JulianSilva2001/PCB-Defects-Detetion-Device/Documentation/CompDefects_live.png

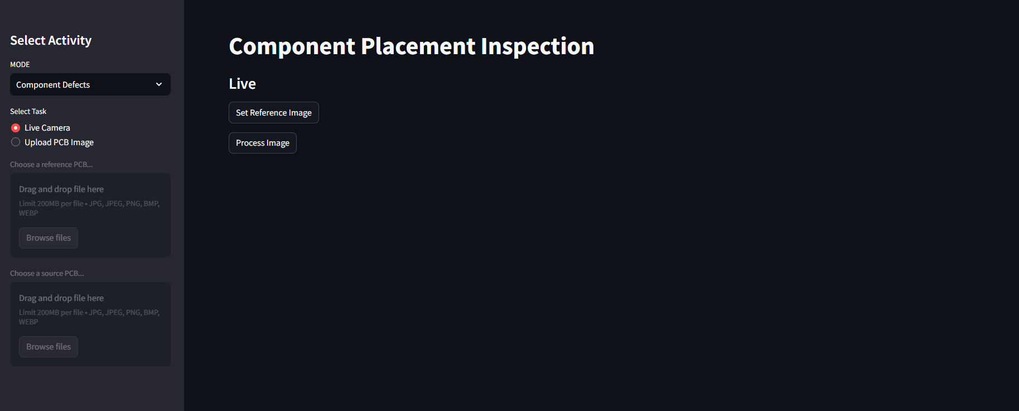
Documentation/CompDefects_live.png
