JulianSilva2001/PCB-Defects-Detetion-Device/Documentation/CompDefects_upload.png

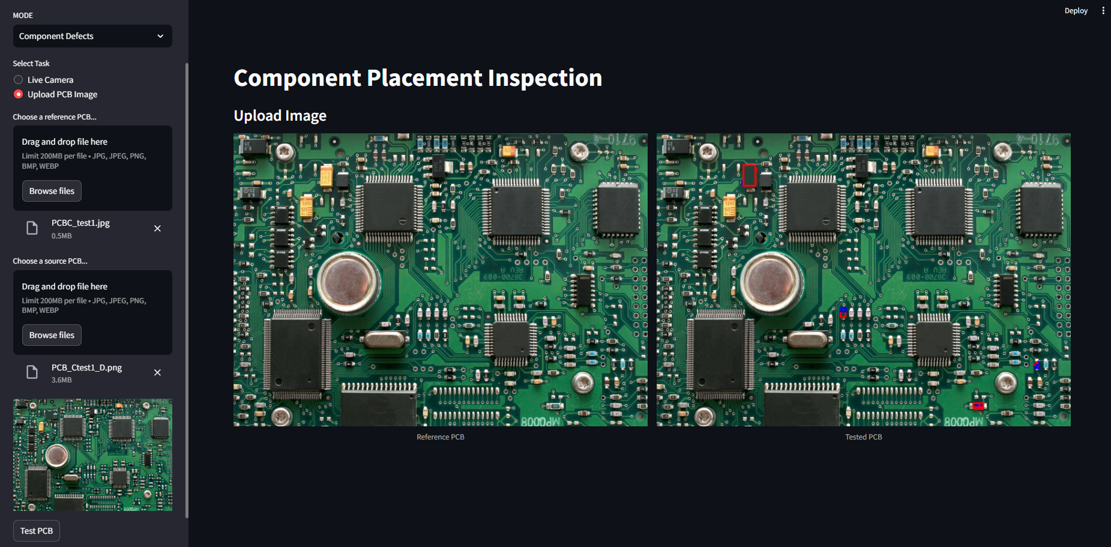
Documentation/CompDefects_upload.png
