JulianSilva2001/PCB-Defects-Detetion-Device/Documentation/Conceptual Design/Enclosure/Enclosure Design A1.jpg

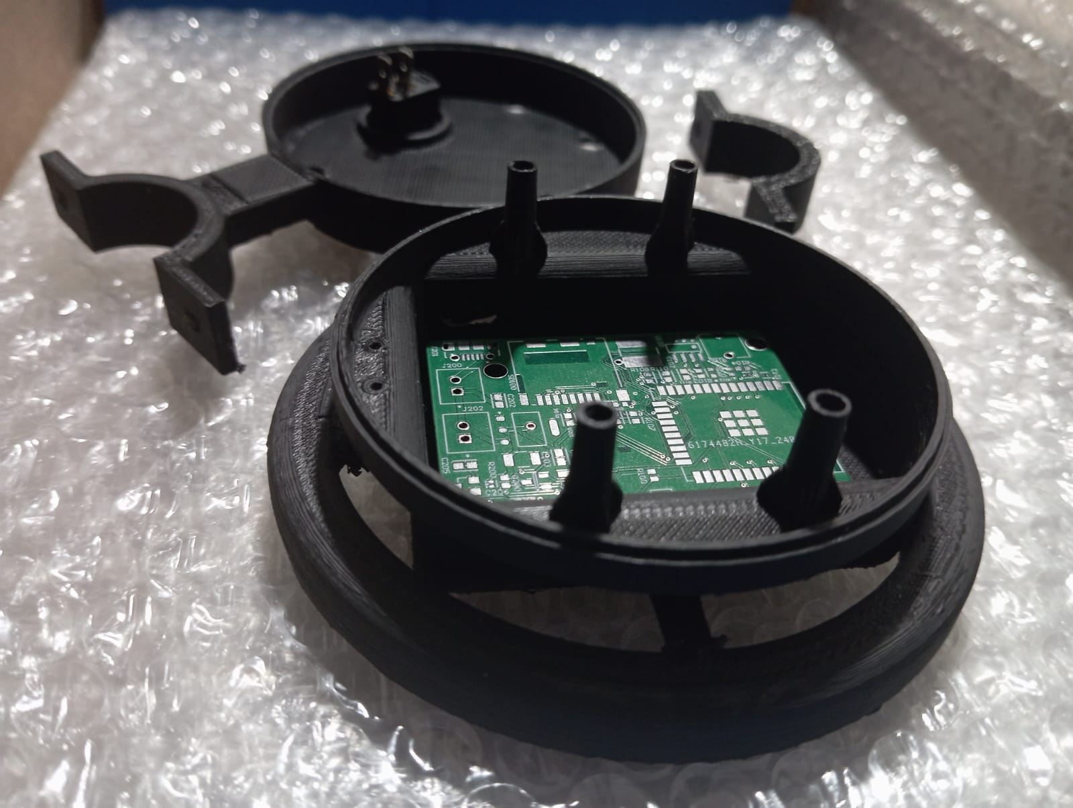
Documentation/Conceptual Design/Enclosure/Enclosure Design A1.jpg
