JulianSilva2001/PCB-Defects-Detetion-Device/Documentation/Conceptual Design/Enclosure/Enclosure Design A4.jpg

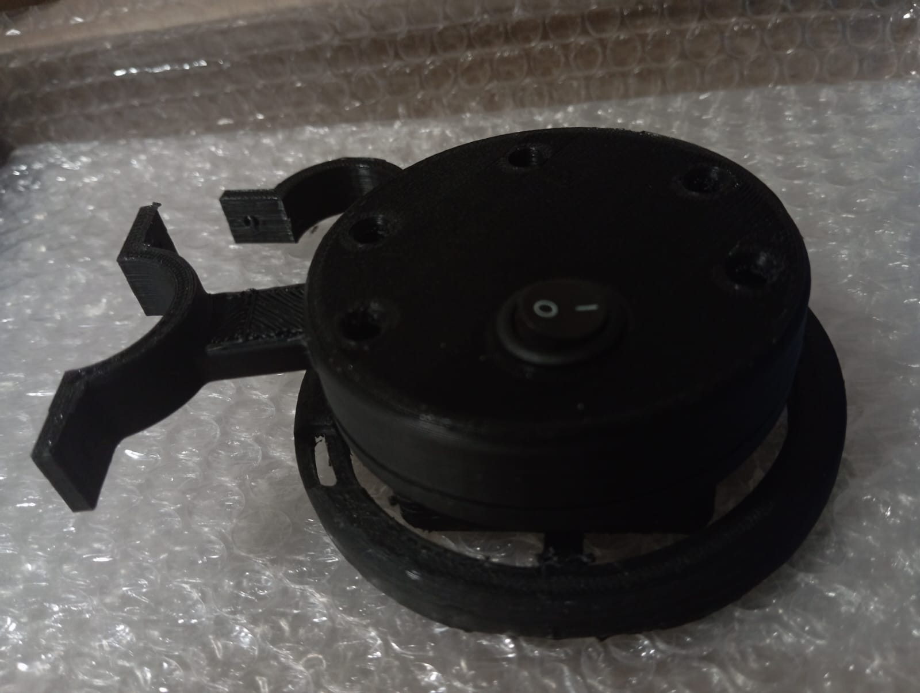
Documentation/Conceptual Design/Enclosure/Enclosure Design A4.jpg
