JulianSilva2001/PCB-Defects-Detetion-Device/Documentation/Conceptual Design/Enclosure/sign.jpg

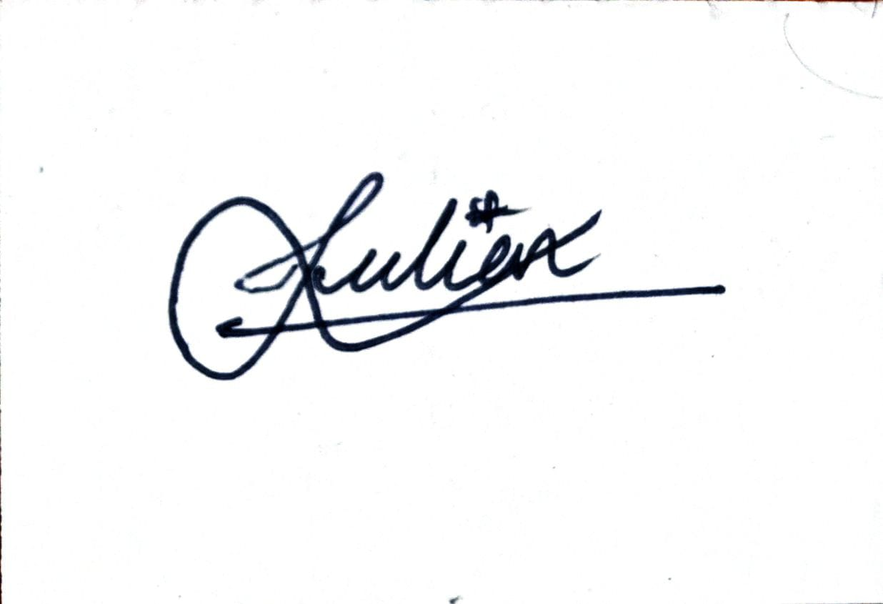
Documentation/Conceptual Design/Enclosure/sign.jpg
