JulianSilva2001/PCB-Defects-Detetion-Device/Documentation/Conceptual Design/Model Tree and Draft Analysis/DraftA1.png

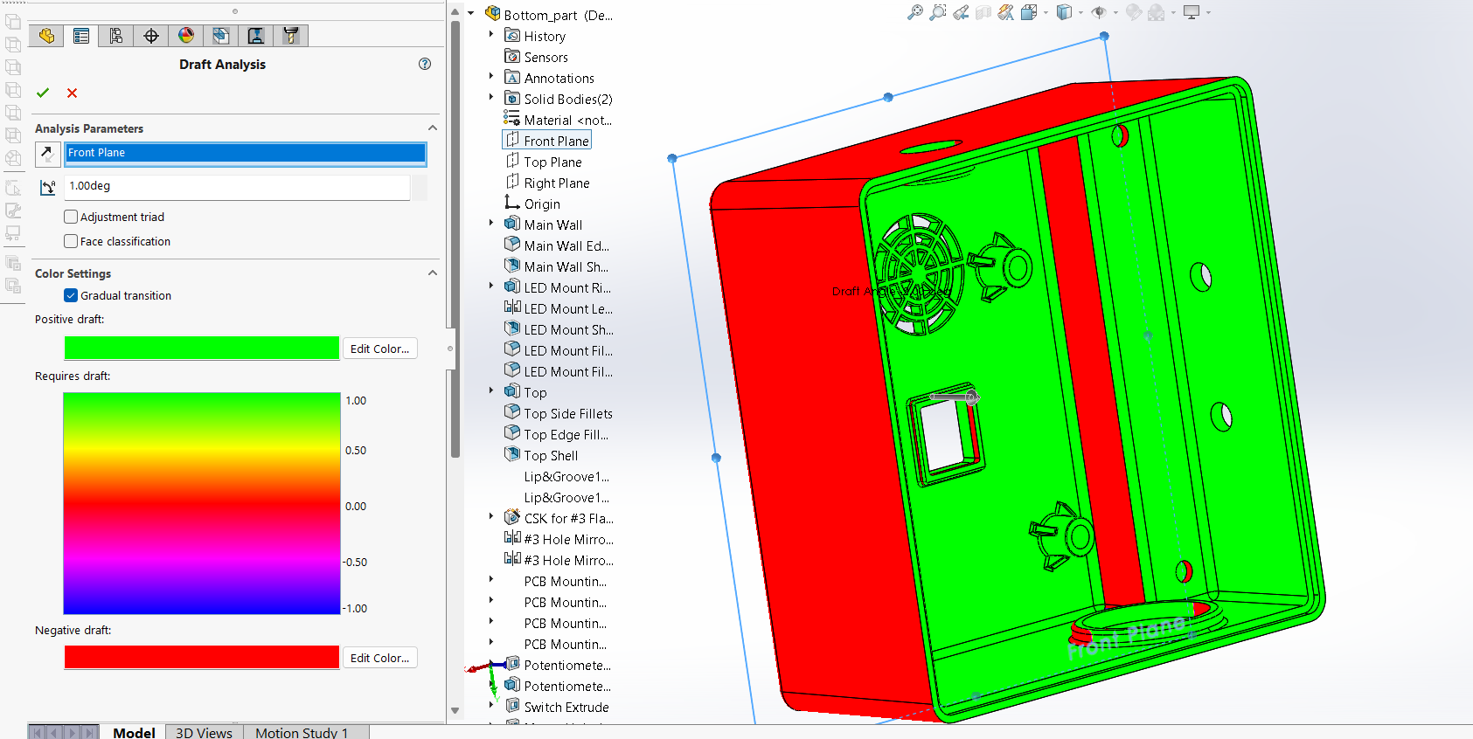
Documentation/Conceptual Design/Model Tree and Draft Analysis/DraftA1.png
