JulianSilva2001/PCB-Defects-Detetion-Device/Documentation/Conceptual Design/Model Tree and Draft Analysis/DraftA2.png

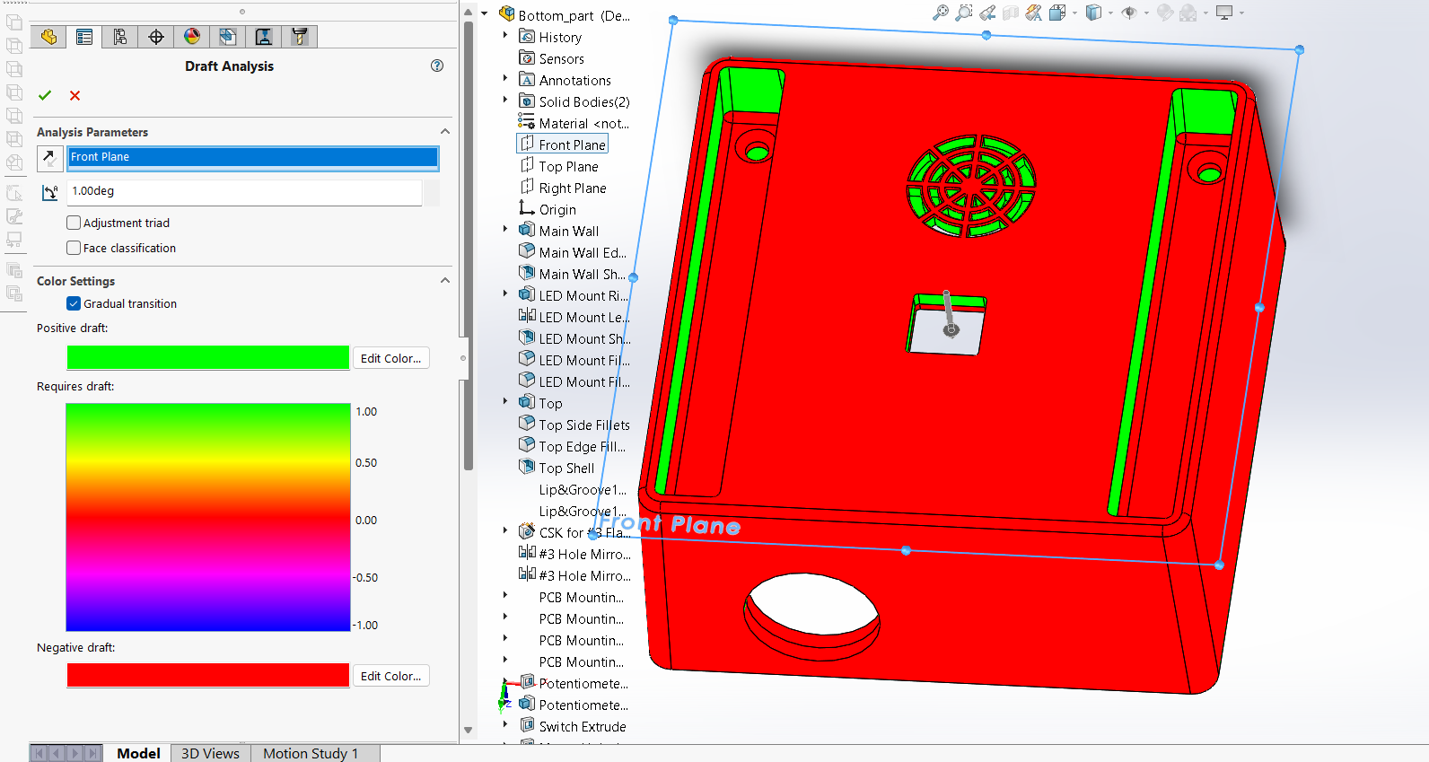
Documentation/Conceptual Design/Model Tree and Draft Analysis/DraftA2.png
