JulianSilva2001/PCB-Defects-Detetion-Device/Documentation/Conceptual Design/Model Tree and Draft Analysis/MT1.png

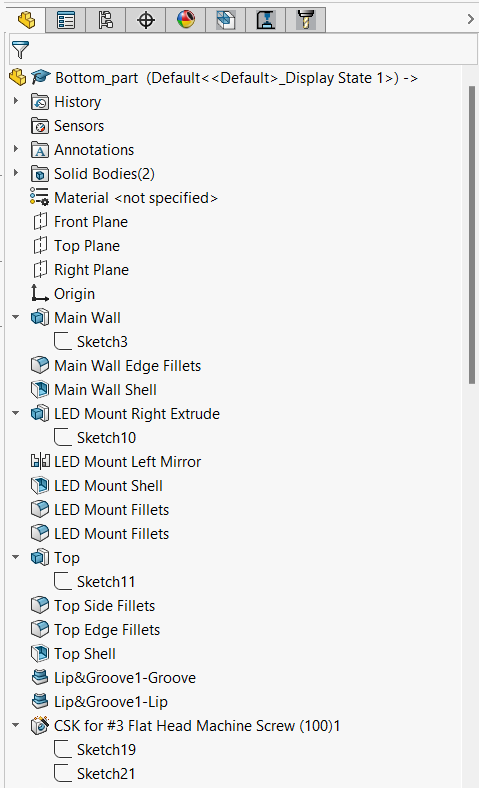
Documentation/Conceptual Design/Model Tree and Draft Analysis/MT1.png
