JulianSilva2001/PCB-Defects-Detetion-Device/Documentation/Conceptual Design/Model Tree and Draft Analysis/MT3.png

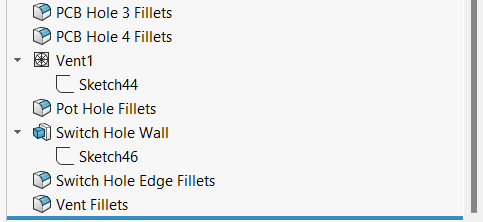
Documentation/Conceptual Design/Model Tree and Draft Analysis/MT3.png
