JulianSilva2001/PCB-Defects-Detetion-Device/Documentation/Conceptual Design/Model Tree and Draft Analysis/Top/Draft A2.png

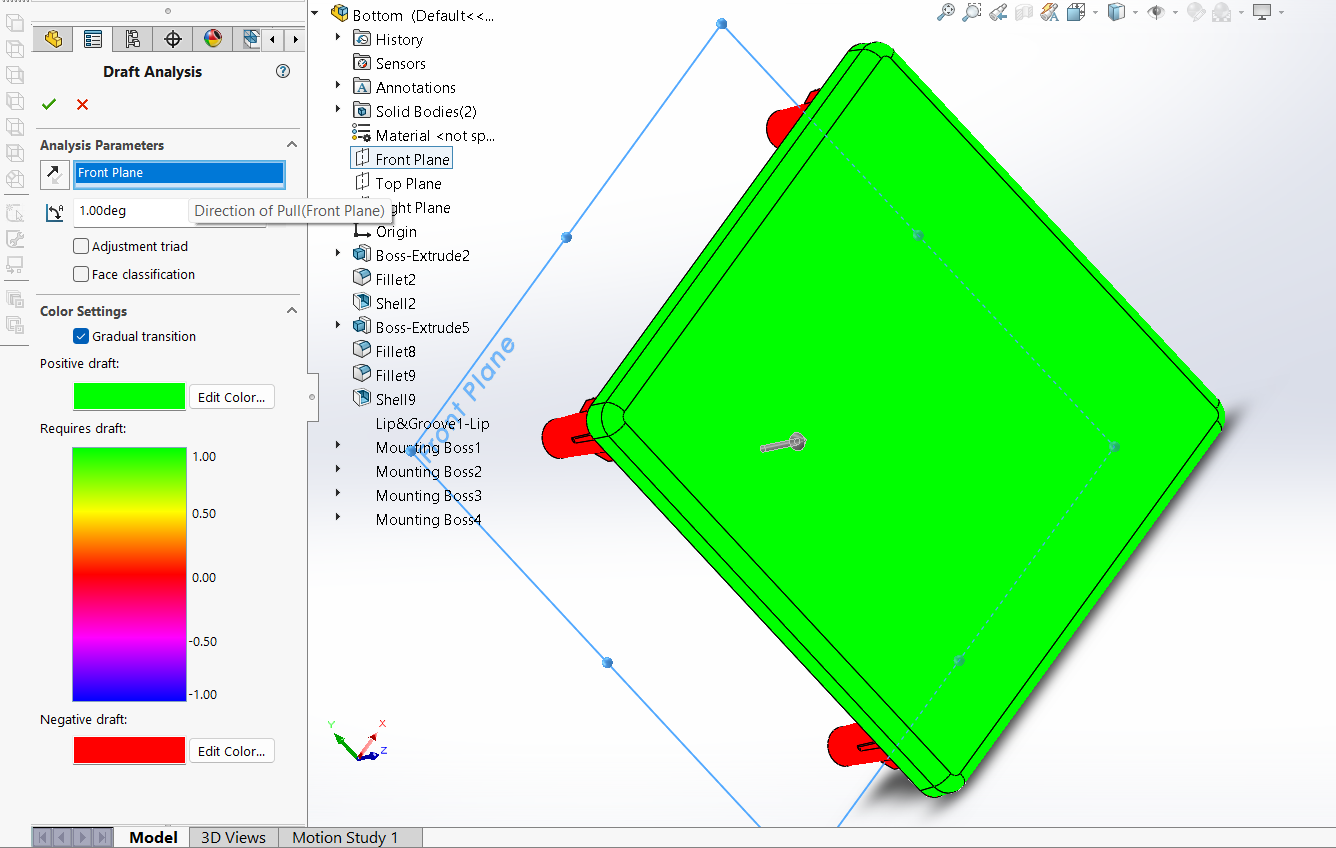
Documentation/Conceptual Design/Model Tree and Draft Analysis/Top/Draft A2.png
