JulianSilva2001/PCB-Defects-Detetion-Device/Documentation/Image Doc/BarePCBs.jpg

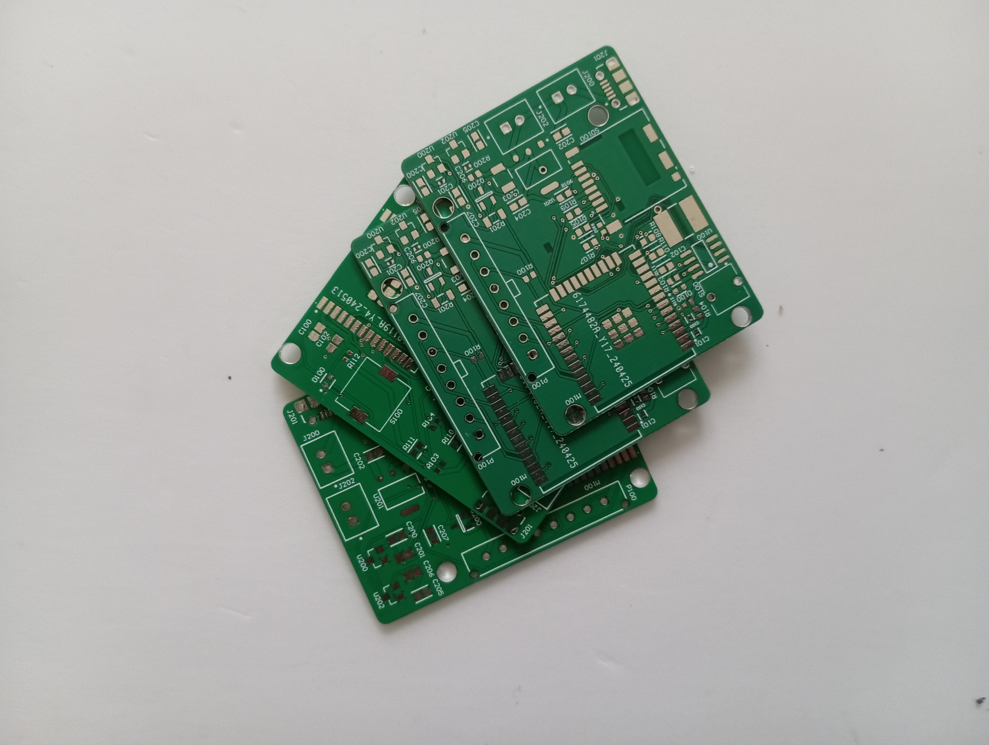
Documentation/Image Doc/BarePCBs.jpg
