JulianSilva2001/PCB-Defects-Detetion-Device/Documentation/Image Doc/BarePCBsSet.jpg

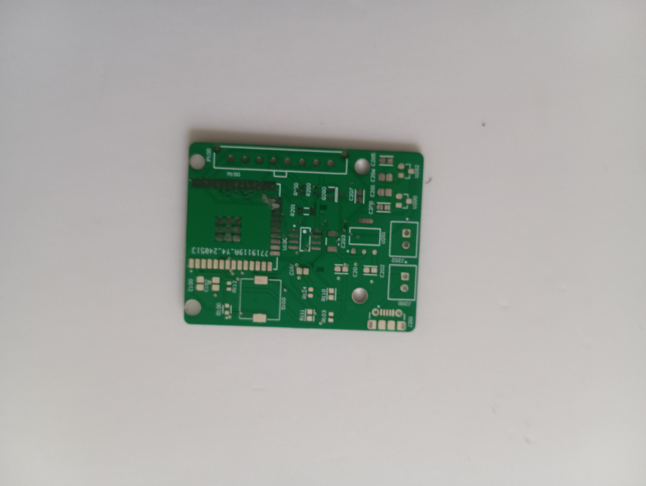
Documentation/Image Doc/BarePCBsSet.jpg
