JulianSilva2001/PCB-Defects-Detetion-Device/Documentation/Image Doc/BarePCBsStensil.jpg

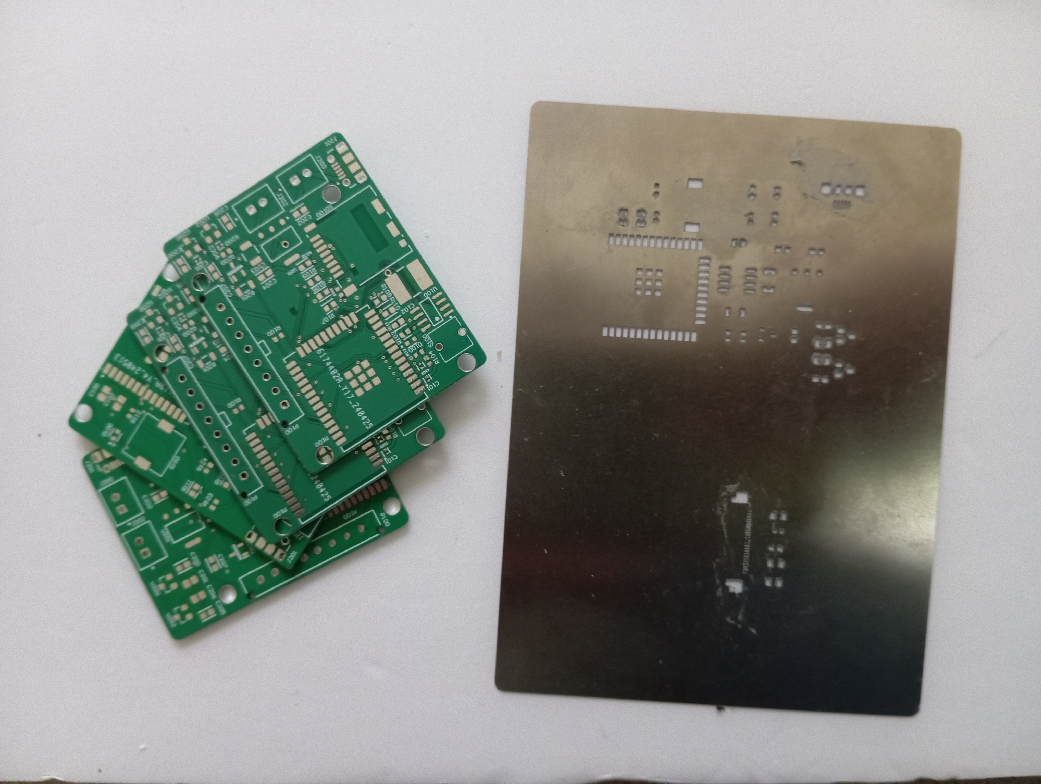
Documentation/Image Doc/BarePCBsStensil.jpg
