JulianSilva2001/PCB-Defects-Detetion-Device/Documentation/Image Doc/BarePCBtop.jpg

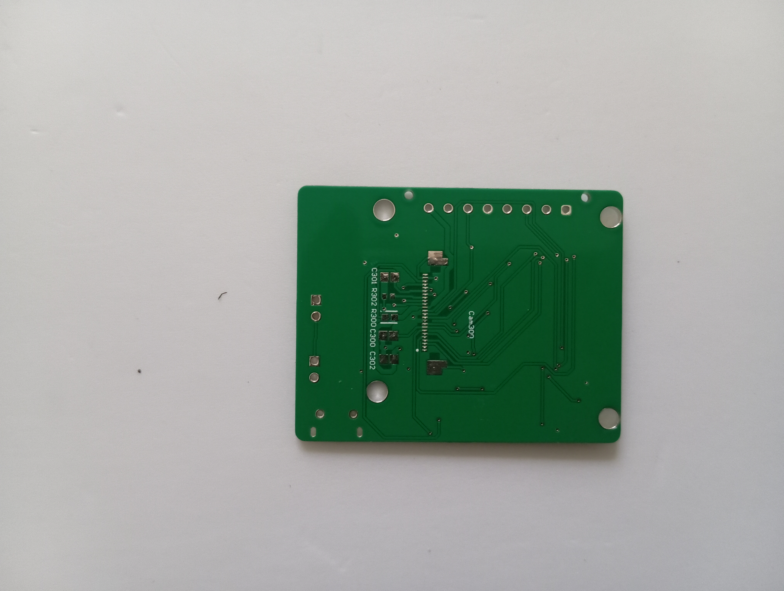
Documentation/Image Doc/BarePCBtop.jpg
