JulianSilva2001/PCB-Defects-Detetion-Device/Documentation/Image Doc/EassebmledSide.jpg

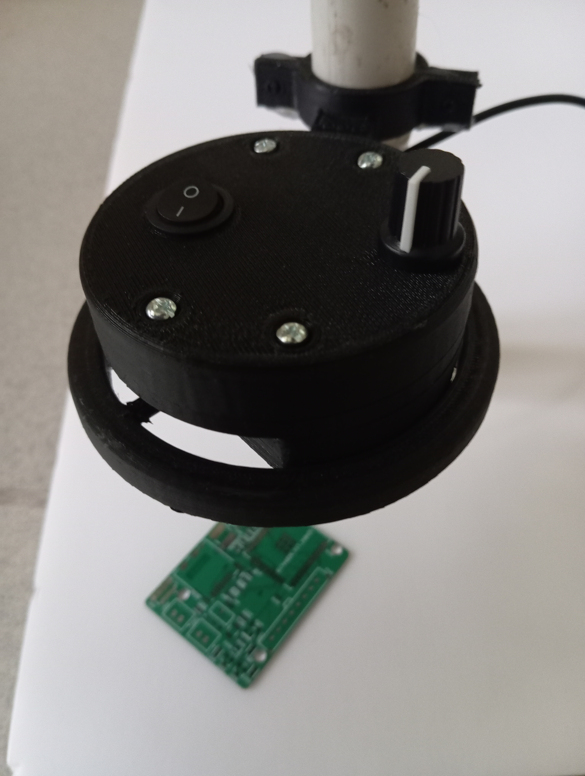
Documentation/Image Doc/EassebmledSide.jpg
