JulianSilva2001/PCB-Defects-Detetion-Device/Documentation/Image Doc/EbottomTop.jpg

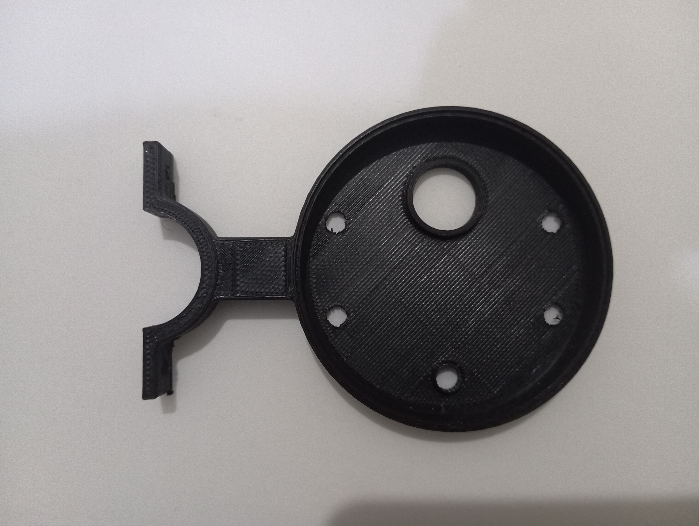
Documentation/Image Doc/EbottomTop.jpg
