JulianSilva2001/PCB-Defects-Detetion-Device/Documentation/Image Doc/EnclosuretopBottom.jpg

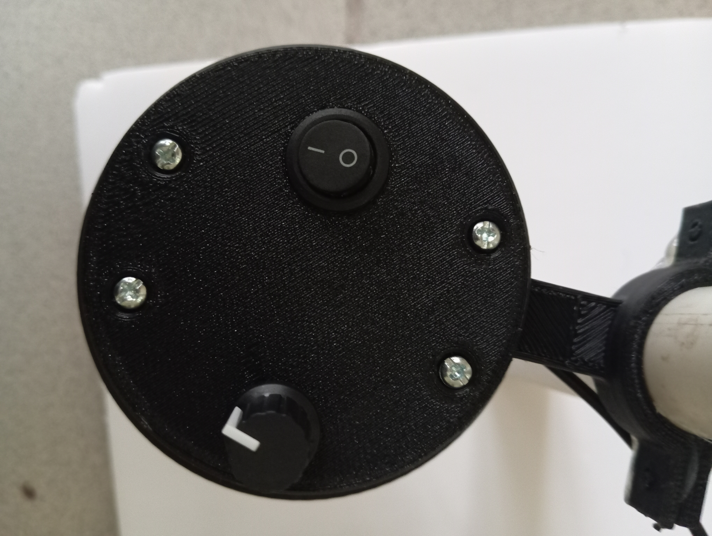
Documentation/Image Doc/EnclosuretopBottom.jpg
