JulianSilva2001/PCB-Defects-Detetion-Device/Documentation/Image Doc/enclosuretopTop.jpg

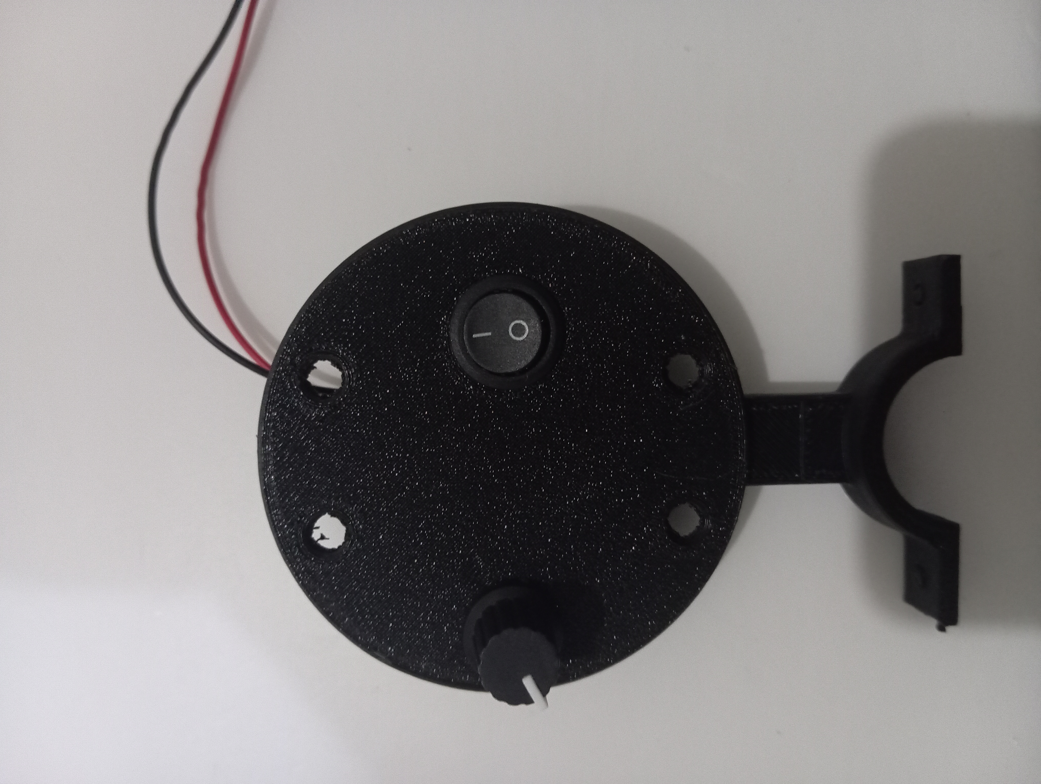
Documentation/Image Doc/enclosuretopTop.jpg
