JulianSilva2001/PCB-Defects-Detetion-Device/Documentation/Image Doc/EnclosureWithlap2.jpg

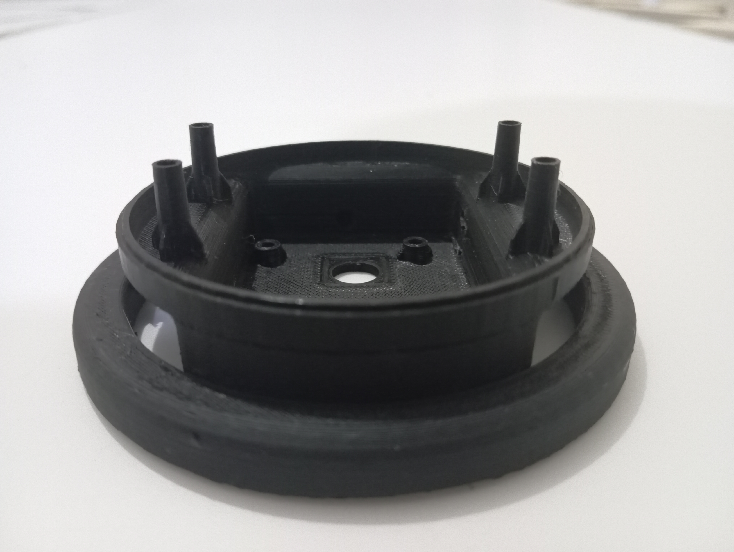
Documentation/Image Doc/EnclosureWithlap2.jpg
