JulianSilva2001/PCB-Defects-Detetion-Device/Documentation/Image Doc/enlcosure.jpg

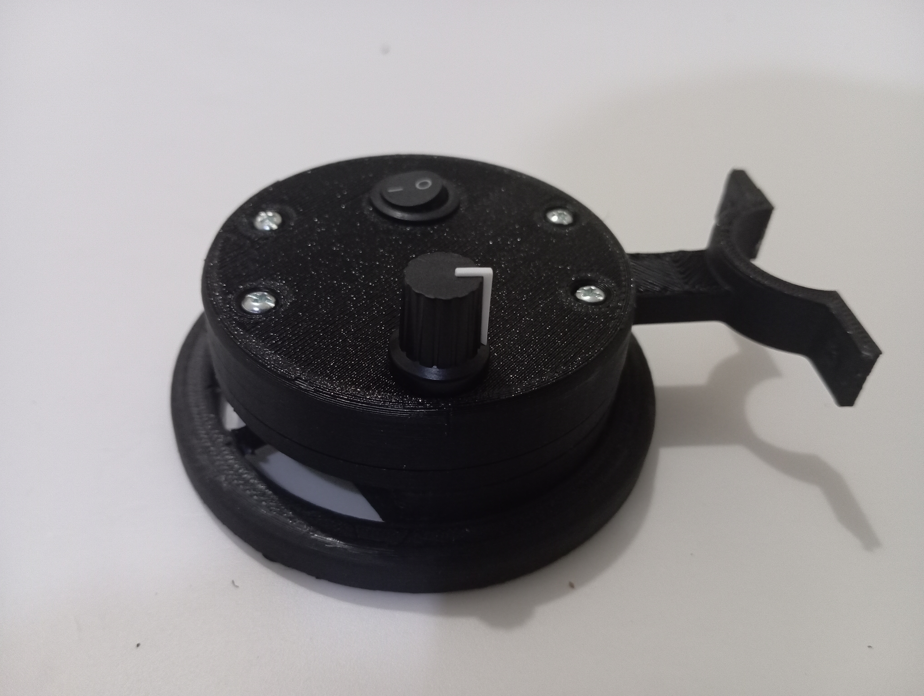
Documentation/Image Doc/enlcosure.jpg
