JulianSilva2001/PCB-Defects-Detetion-Device/Documentation/Image Doc/EpartsFull.jpg

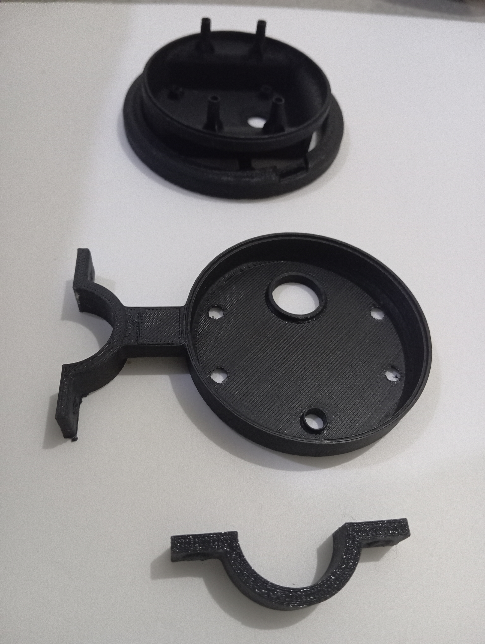
Documentation/Image Doc/EpartsFull.jpg
