JulianSilva2001/PCB-Defects-Detetion-Device/Documentation/Image Doc/EtopSide.jpg

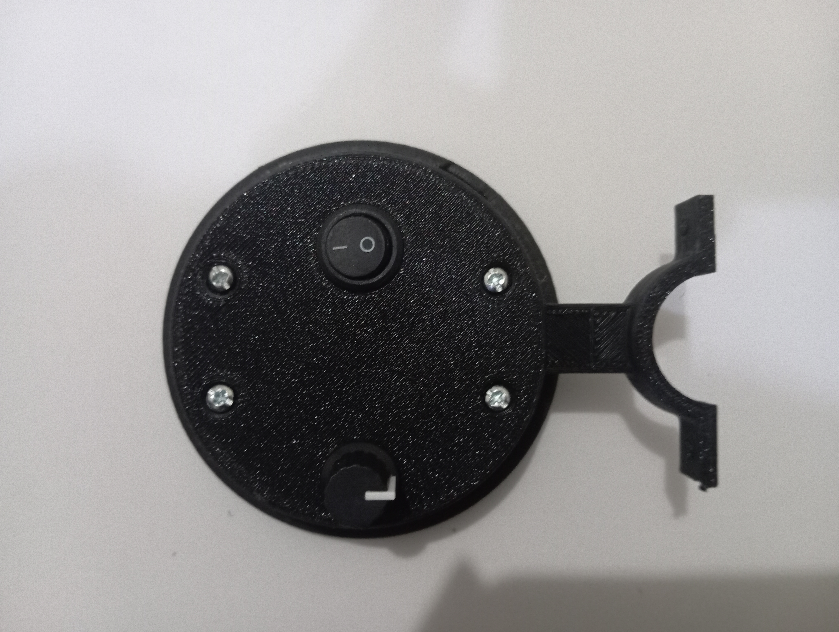
Documentation/Image Doc/EtopSide.jpg
