JulianSilva2001/PCB-Defects-Detetion-Device/Documentation/Image Doc/EtopTop.jpg

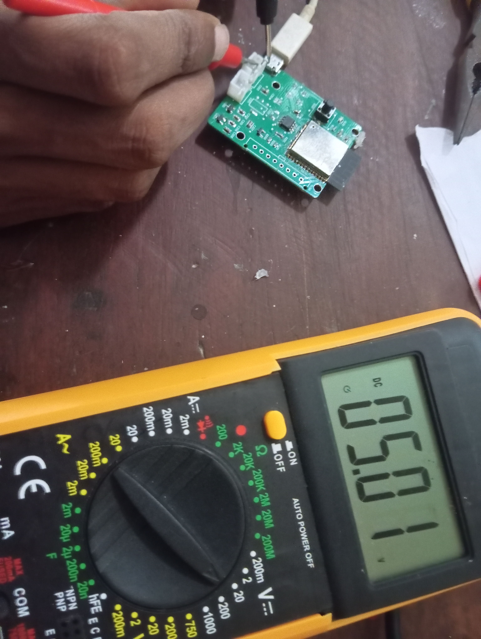
Documentation/Image Doc/EtopTop.jpg
