JulianSilva2001/PCB-Defects-Detetion-Device/Documentation/Image Doc/FullEnclosure.jpg

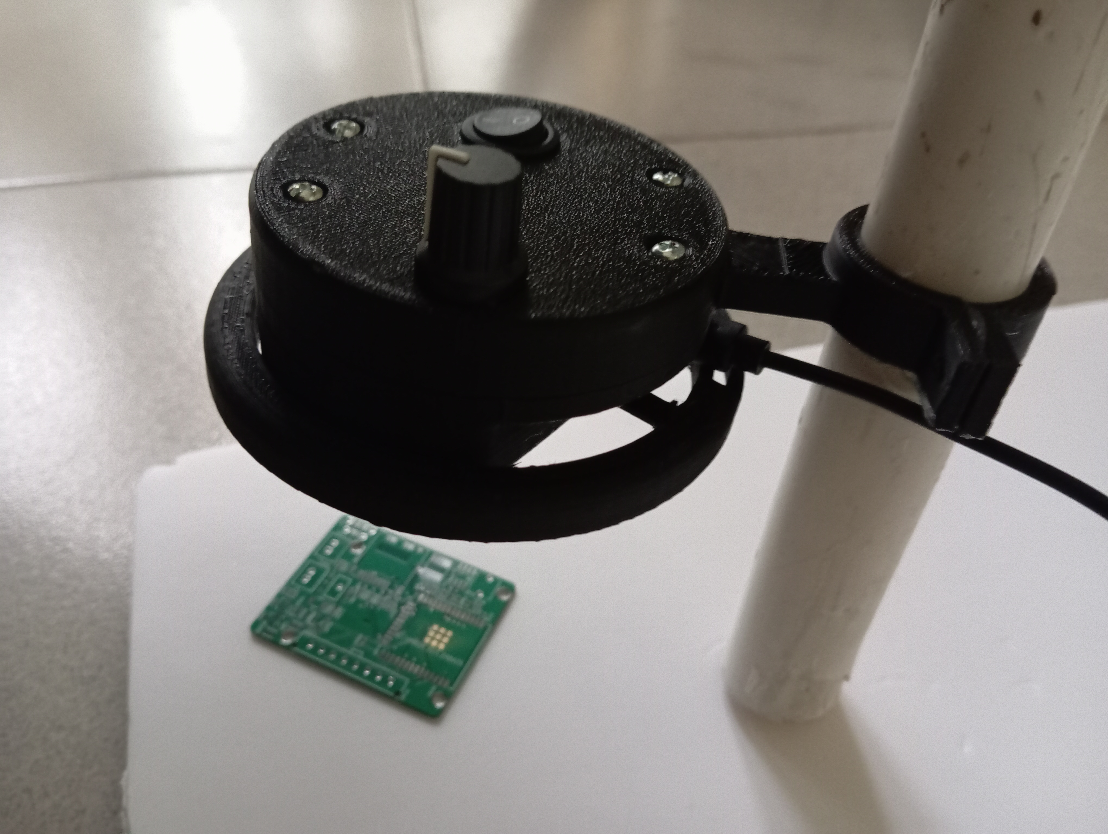
Documentation/Image Doc/FullEnclosure.jpg
