JulianSilva2001/PCB-Defects-Detetion-Device/Documentation/Image Doc/IMG_20240706_085507.jpg

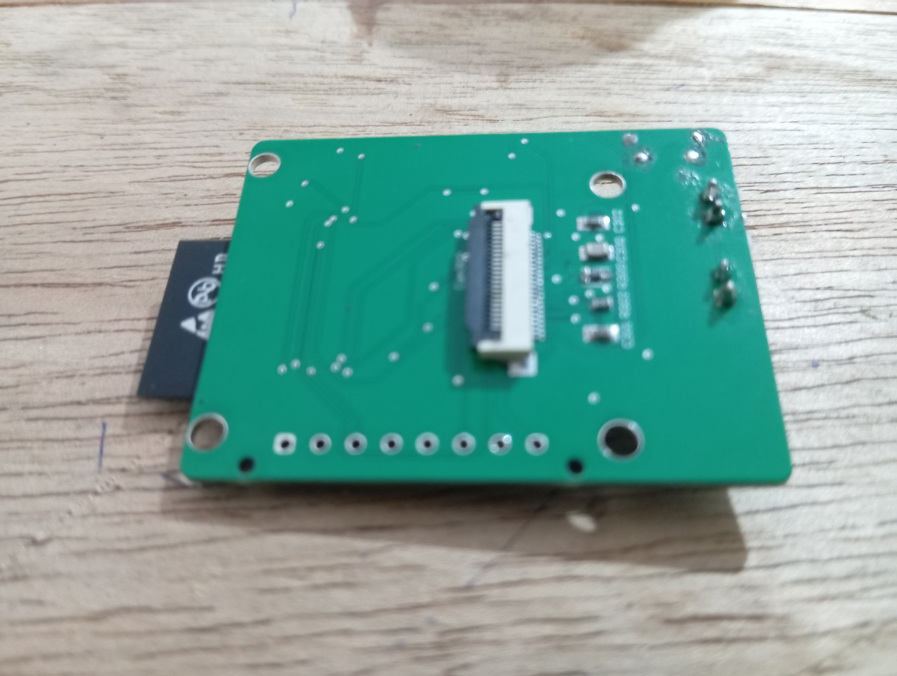
Documentation/Image Doc/IMG_20240706_085507.jpg
