JulianSilva2001/PCB-Defects-Detetion-Device/Documentation/Methodology/aoi.png

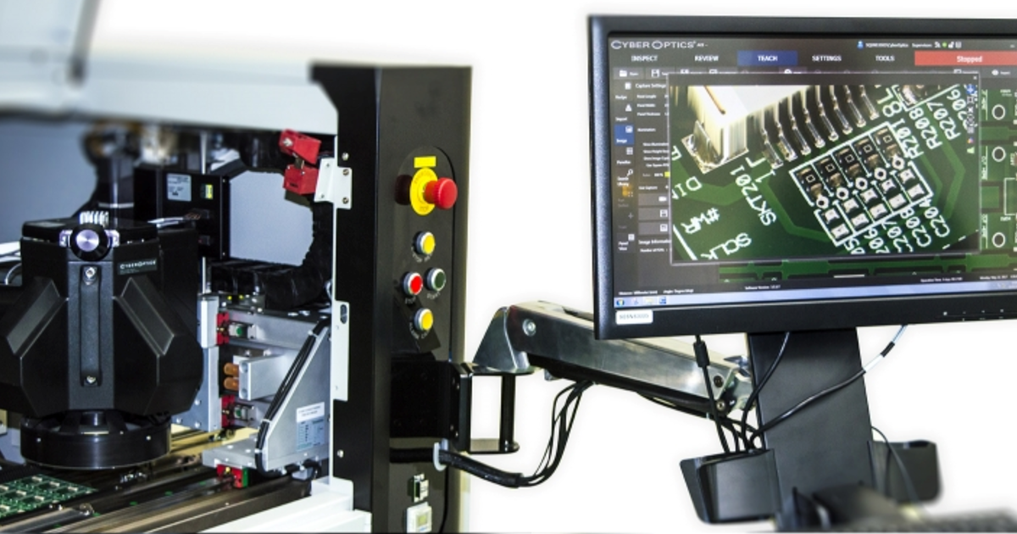
Documentation/Methodology/aoi.png
