JulianSilva2001/PCB-Defects-Detetion-Device/Documentation/Methodology/Conceptual Design/CD_portable.jpg

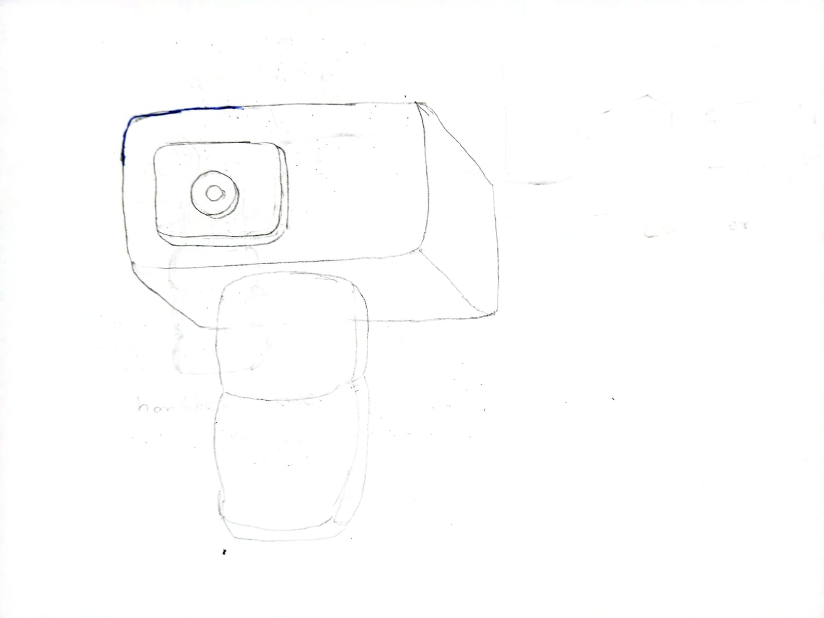
Documentation/Methodology/Conceptual Design/CD_portable.jpg
