JulianSilva2001/PCB-Defects-Detetion-Device/Documentation/Methodology/Conceptual Design/FD_Comp.jpg

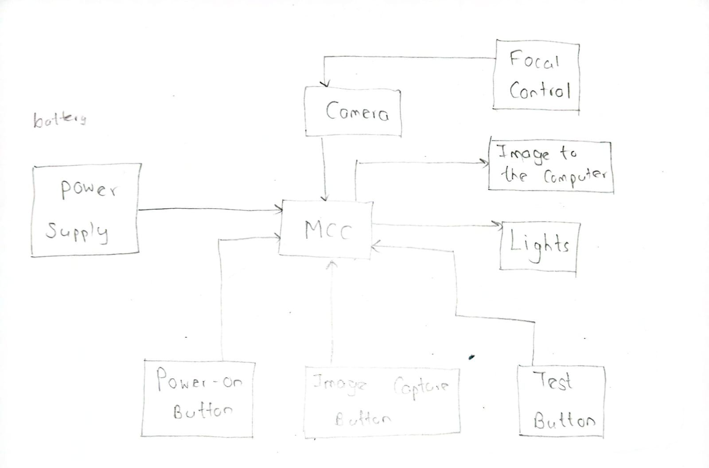
Documentation/Methodology/Conceptual Design/FD_Comp.jpg
