JulianSilva2001/PCB-Defects-Detetion-Device/Documentation/Methodology/Conceptual Design/FD_Portable.jpg

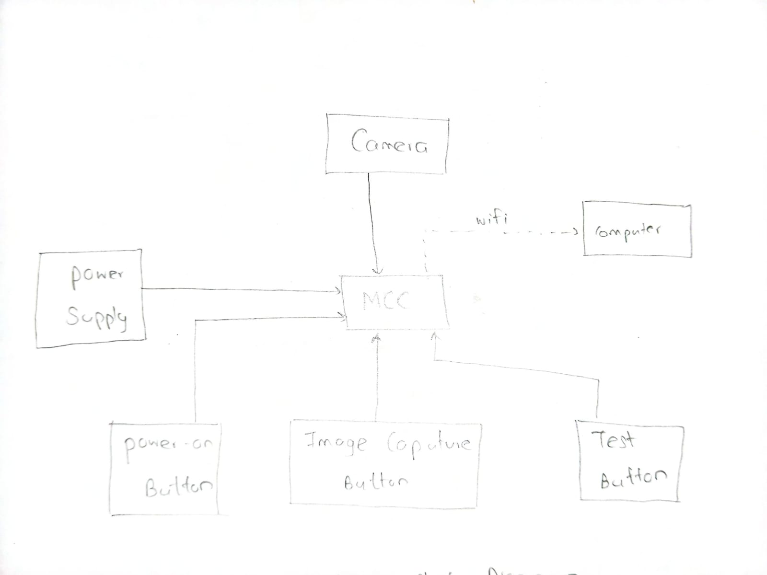
Documentation/Methodology/Conceptual Design/FD_Portable.jpg
