JulianSilva2001/PCB-Defects-Detetion-Device/Documentation/Methodology/maxresdefault (1).jpg

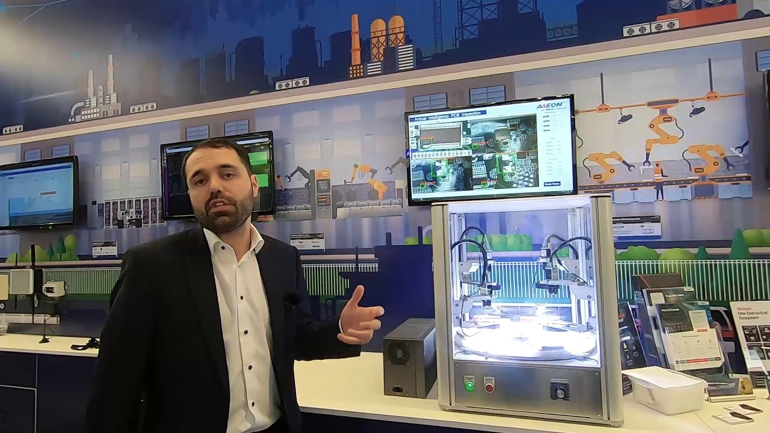
Documentation/Methodology/maxresdefault (1).jpg
