JulianSilva2001/PCB-Defects-Detetion-Device/Documentation/Methodology/maxresdefault.jpg

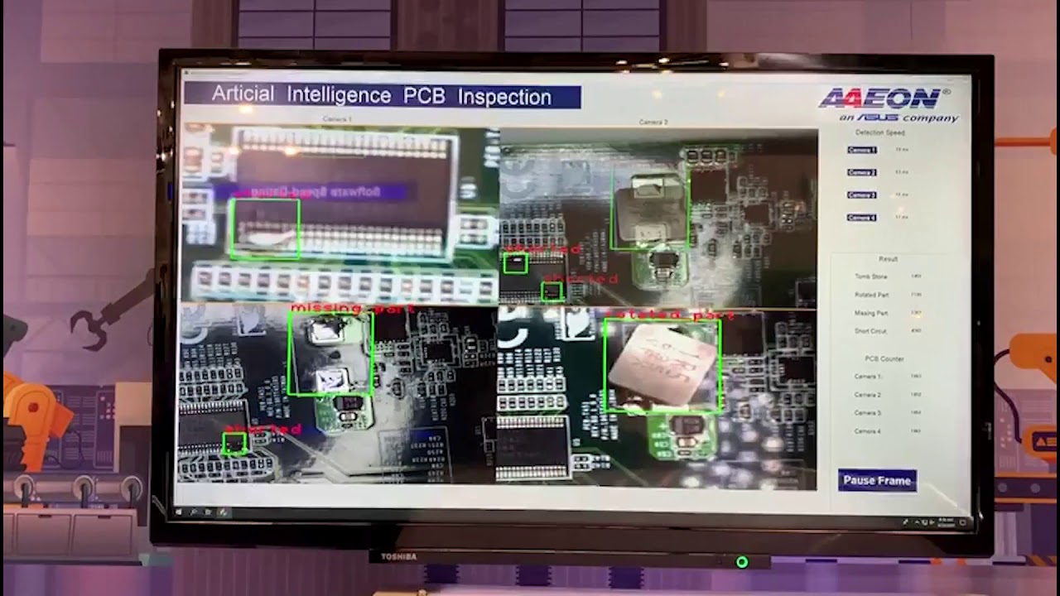
Documentation/Methodology/maxresdefault.jpg
