JulianSilva2001/PCB-Defects-Detetion-Device/Documentation/Methodology/MV-6_OMNI_3D_AOI_Series.jpg

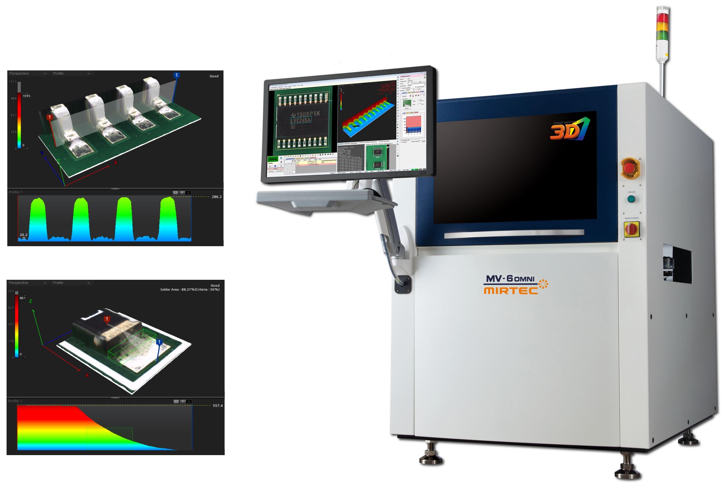
Documentation/Methodology/MV-6_OMNI_3D_AOI_Series.jpg
