JulianSilva2001/PCB-Defects-Detetion-Device/Documentation/Methodology/ourDevice.png

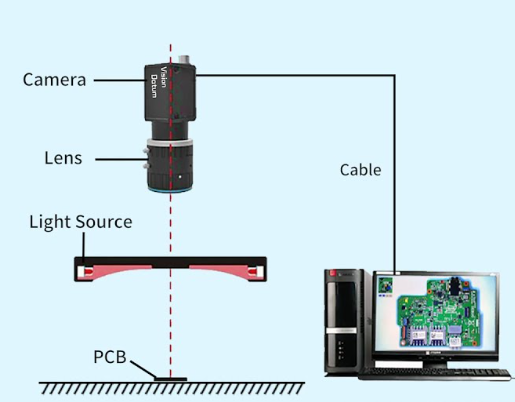
Documentation/Methodology/ourDevice.png
