JulianSilva2001/PCB-Defects-Detetion-Device/Documentation/PCBdefects_live.png

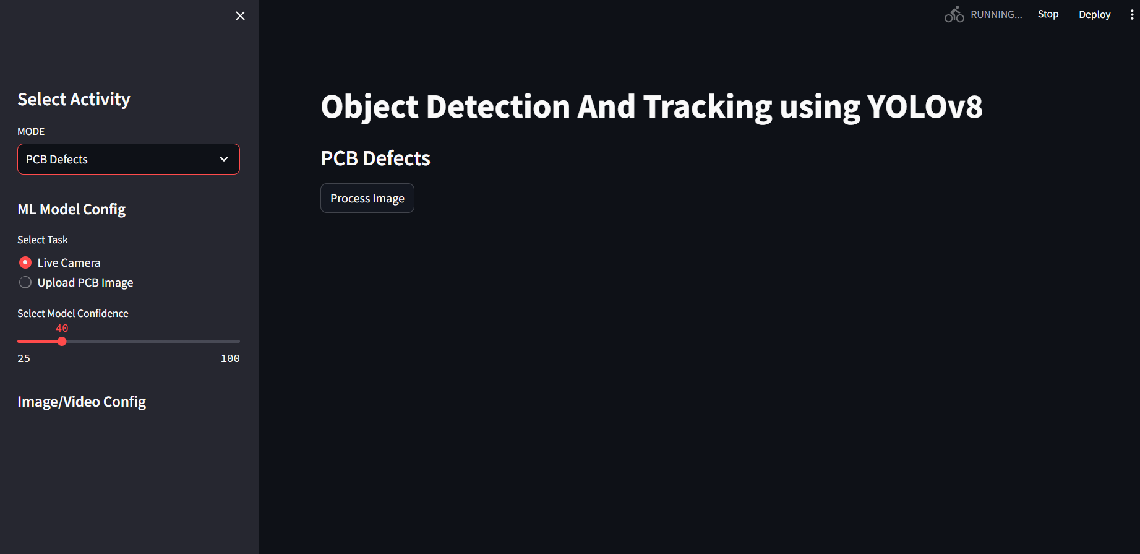
Documentation/PCBdefects_live.png
