JulianSilva2001/PCB-Defects-Detetion-Device/Documentation/Screenshot 2024-06-02 133222.png

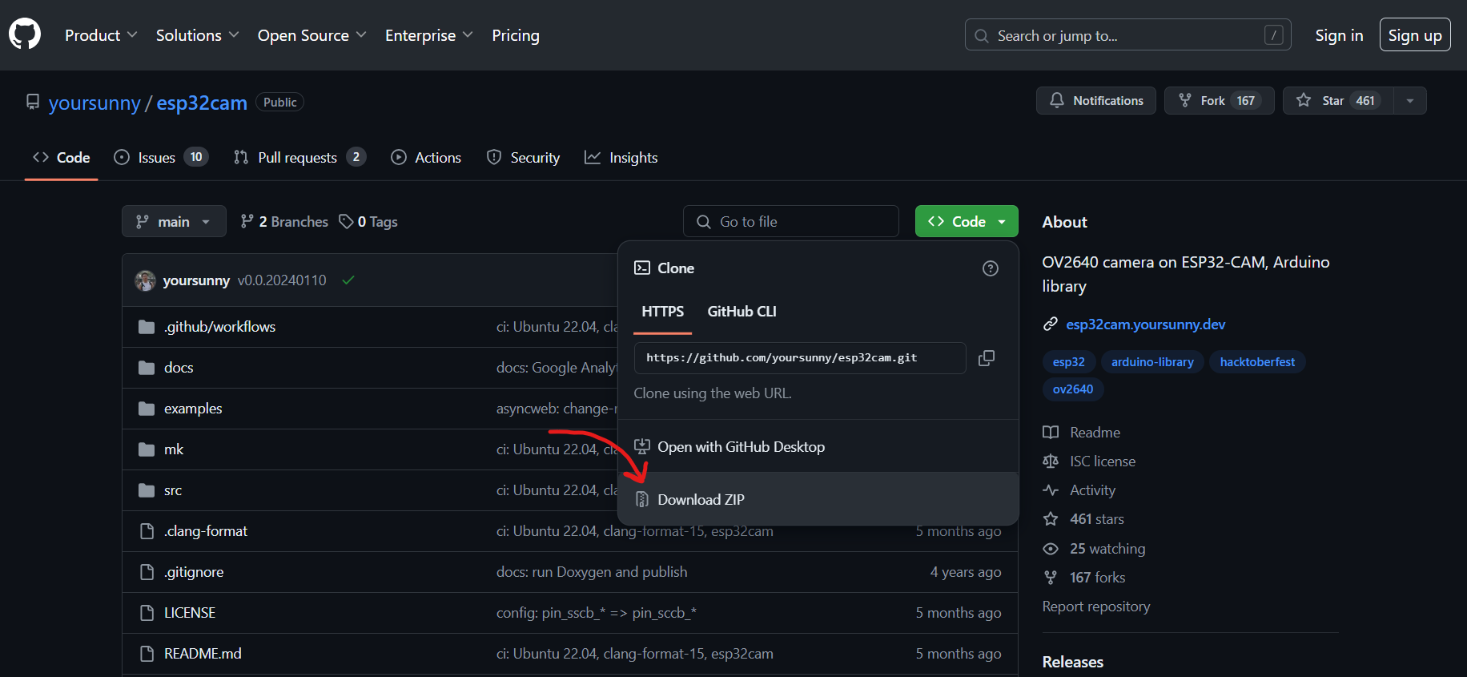
Documentation/Screenshot 2024-06-02 133222.png
