JulianSilva2001/PCB-Defects-Detetion-Device/Documentation/Serial-ESP32-CAM-Data.png

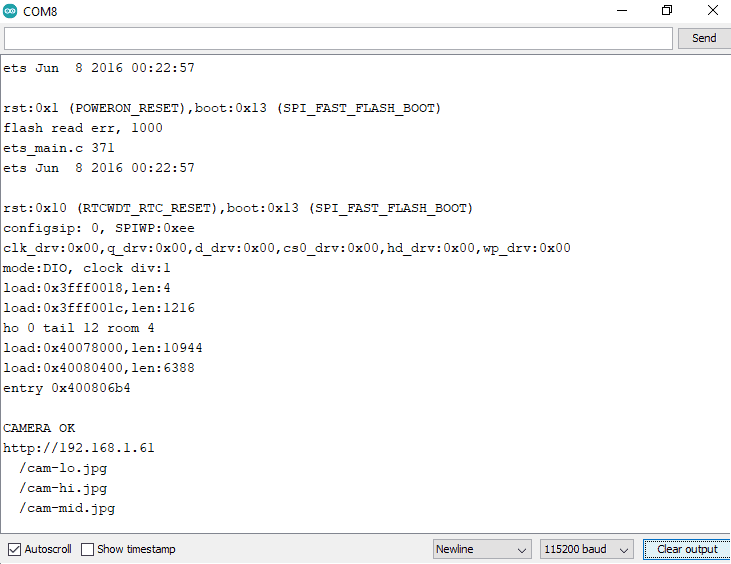
Documentation/Serial-ESP32-CAM-Data.png
