JulianSilva2001/PCB-Defects-Detetion-Device/code/Test Images/Component Deffects/A2/ref.png

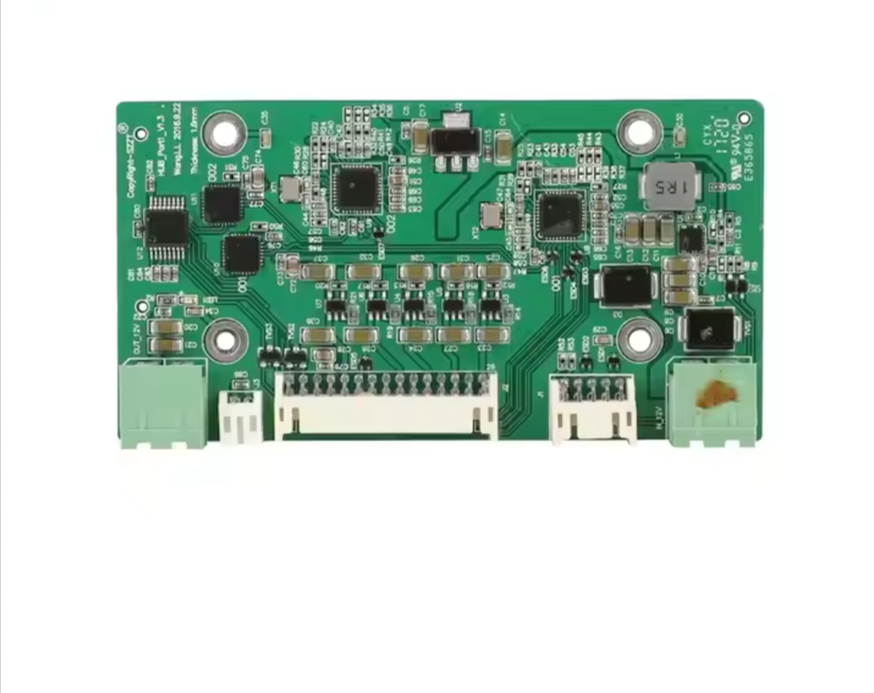
code/Test Images/Component Deffects/A2/ref.png
