JulianSilva2001/PCB-Defects-Detetion-Device/code/Test Images/Component Deffects/A2/source.png

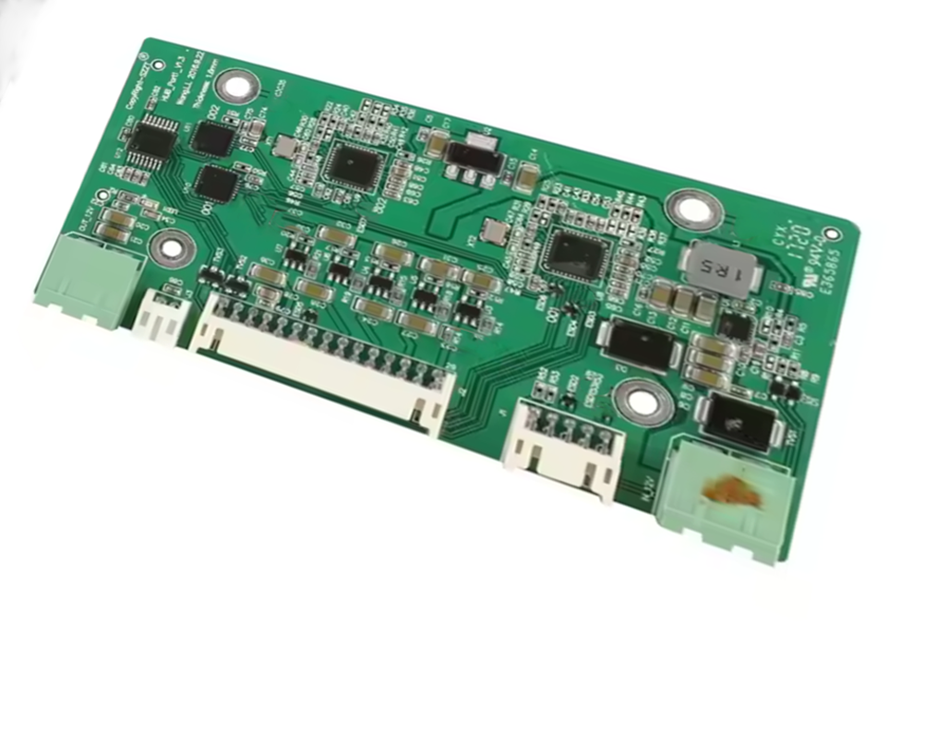
code/Test Images/Component Deffects/A2/source.png
