JulianSilva2001/PCB-Defects-Detetion-Device/code/Test Images/Component Deffects/anamoly_2/Screenshot 2025-01-14 001653.png

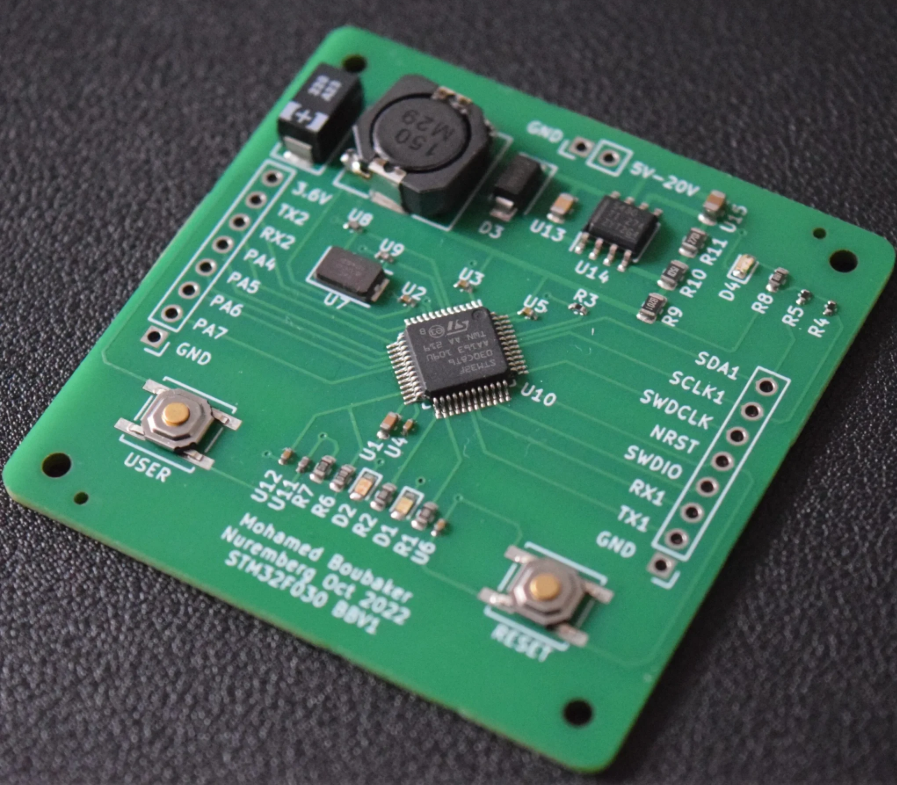
code/Test Images/Component Deffects/anamoly_2/Screenshot 2025-01-14 001653.png
