JulianSilva2001/PCB-Defects-Detetion-Device/code/Test Images/Component Deffects/warped_image.jpg

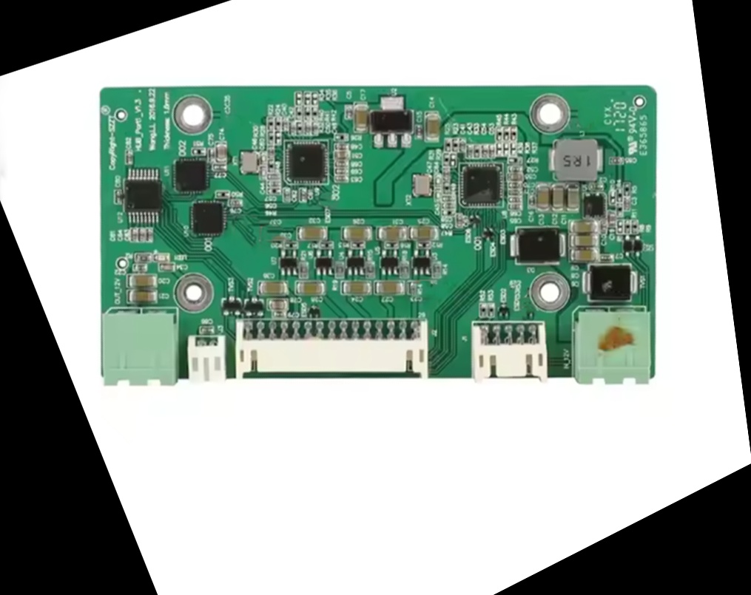
code/Test Images/Component Deffects/warped_image.jpg
