JulianSilva2001/PCB-Defects-Detetion-Device/Documentation/Conceptual Design/Enclosure/PCB Soldering.jpg

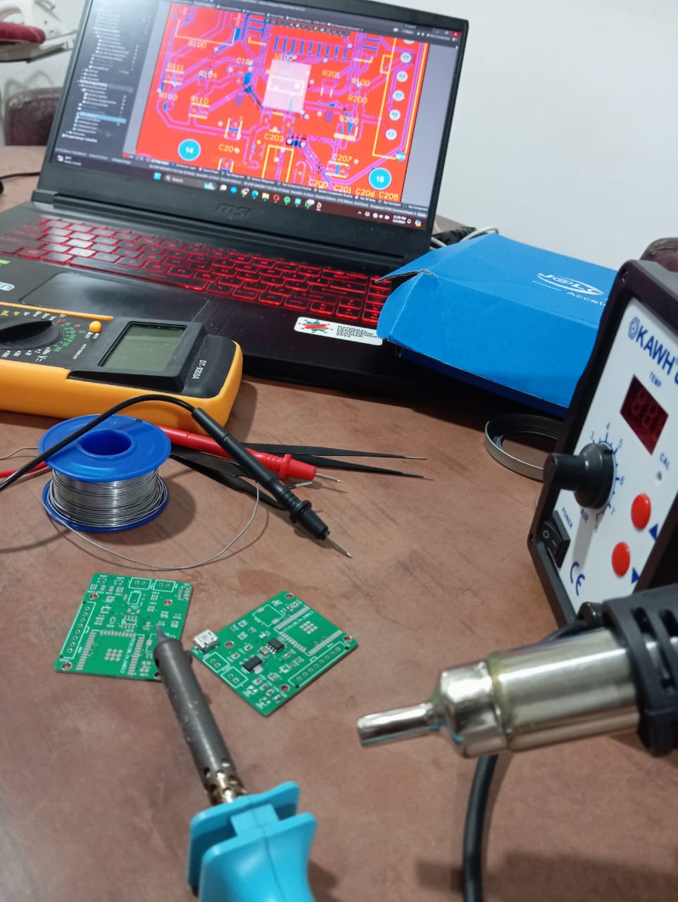
Documentation/Conceptual Design/Enclosure/PCB Soldering.jpg
