JulianSilva2001/PCB-Defects-Detetion-Device/Documentation/Image Doc/solderedPCBFront.jpg

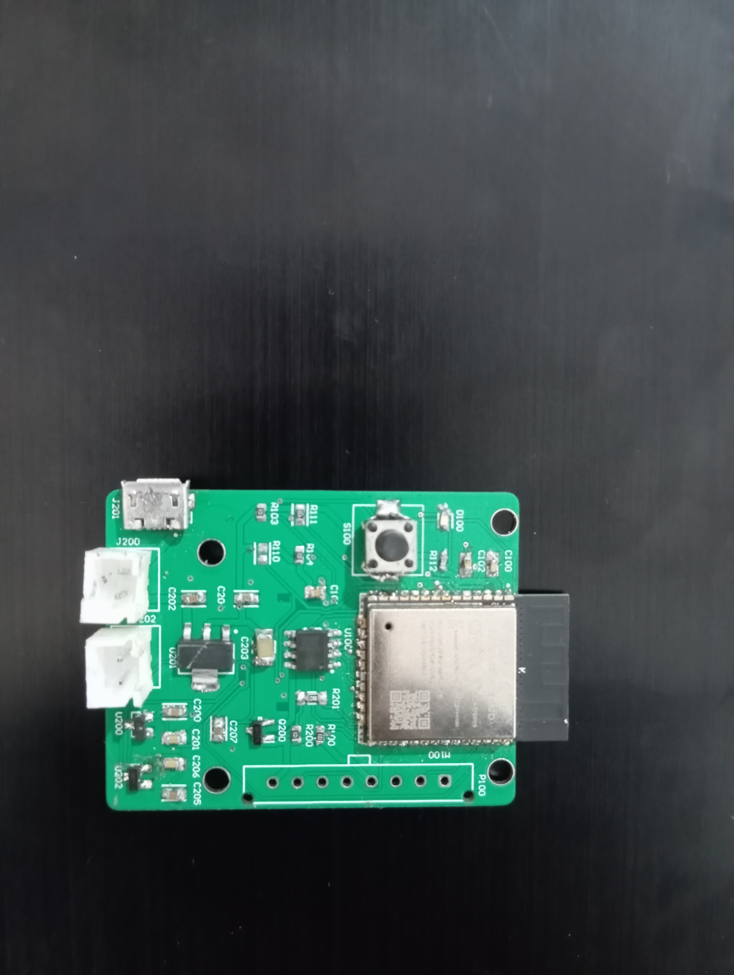
Documentation/Image Doc/solderedPCBFront.jpg
