JulianSilva2001/PCB-Defects-Detetion-Device/Documentation/Image Doc/solderedPCBside.jpg

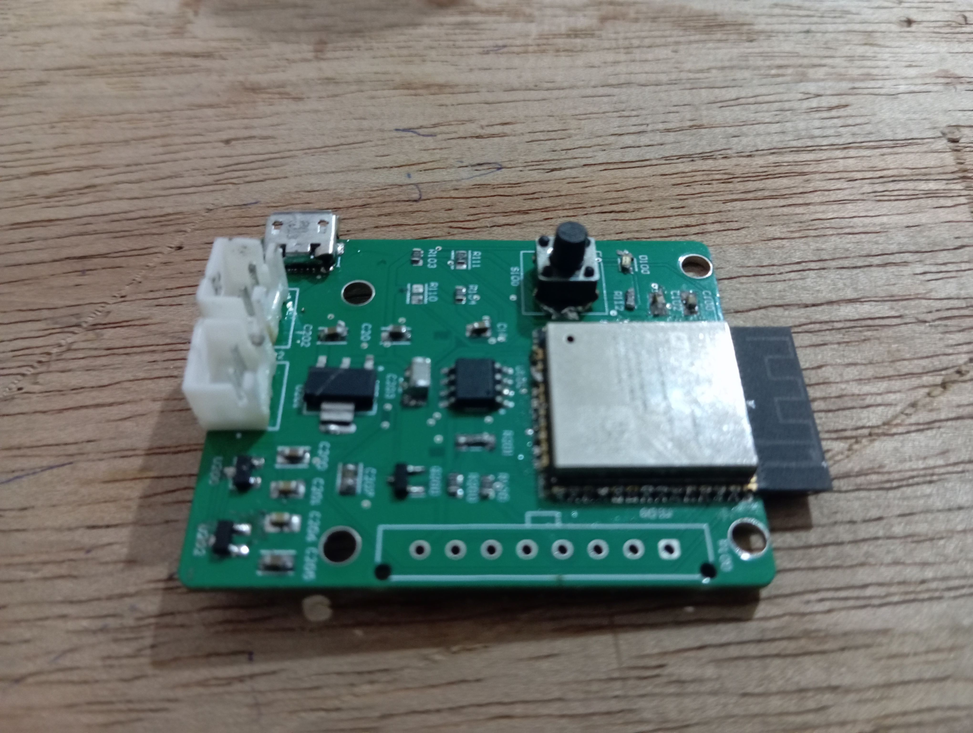
Documentation/Image Doc/solderedPCBside.jpg
