JulianSilva2001/PCB-Defects-Detetion-Device/Documentation/Image Doc/solderedPCBTop.jpg

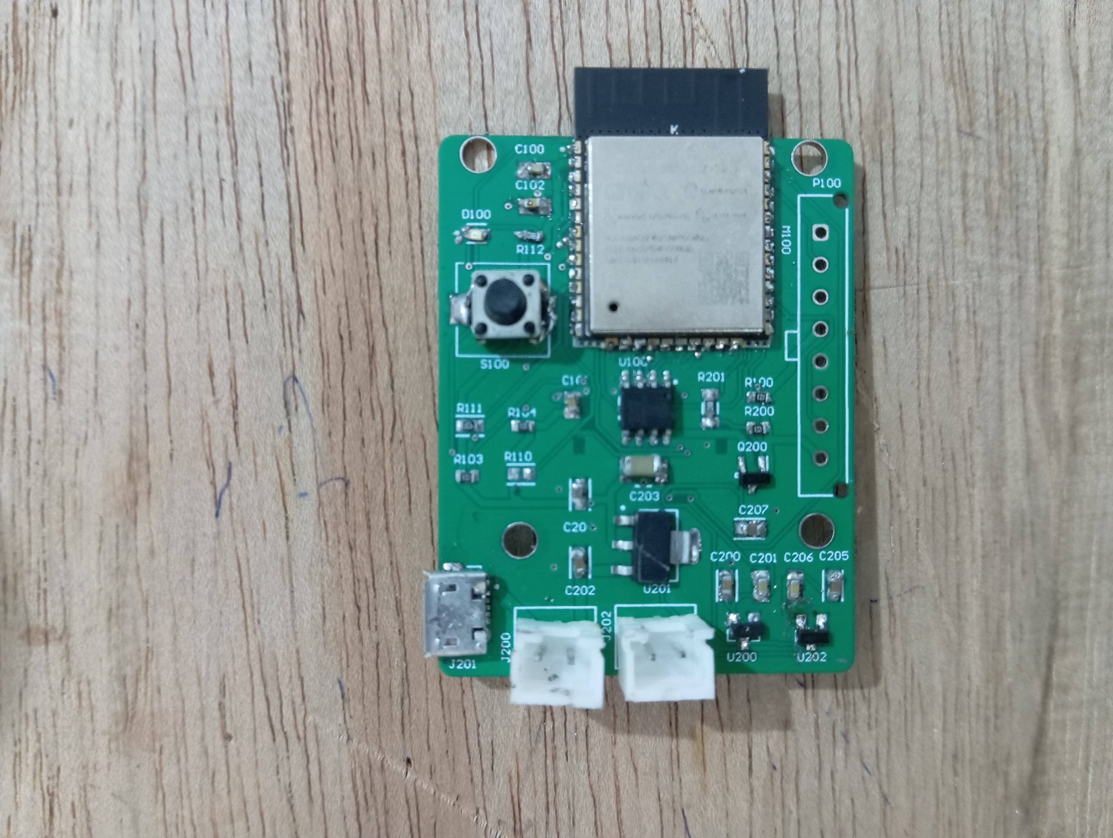
Documentation/Image Doc/solderedPCBTop.jpg
