JulianSilva2001/PCB-Defects-Detetion-Device/code/Test Images/Component Deffects/PCBC_test1_warped.png

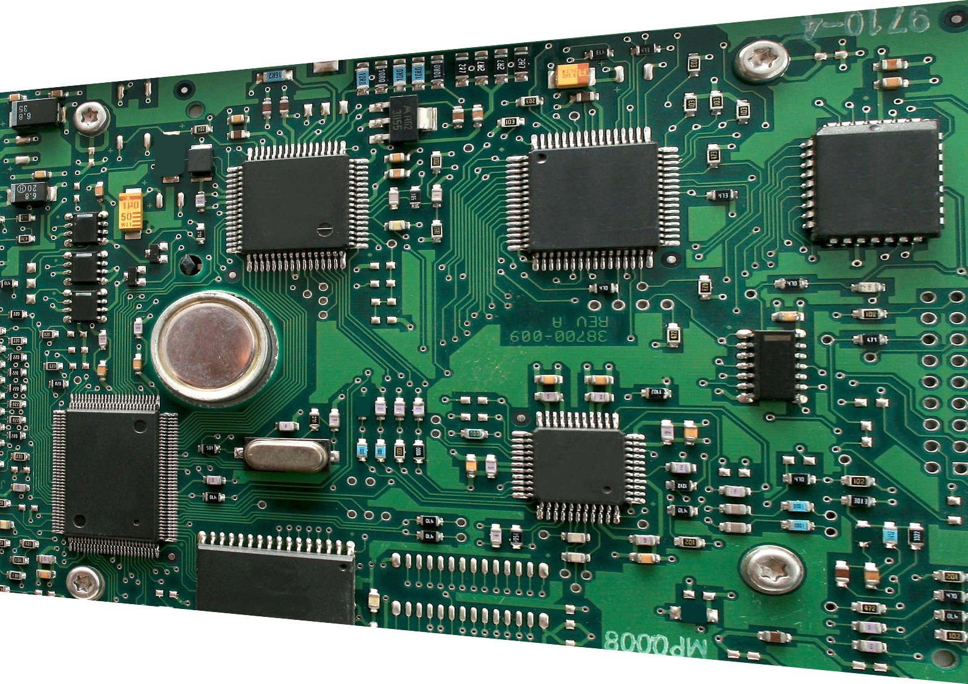
code/Test Images/Component Deffects/PCBC_test1_warped.png
