JulianSilva2001/PCB-Defects-Detetion-Device/code/Test Images/test1.jpg

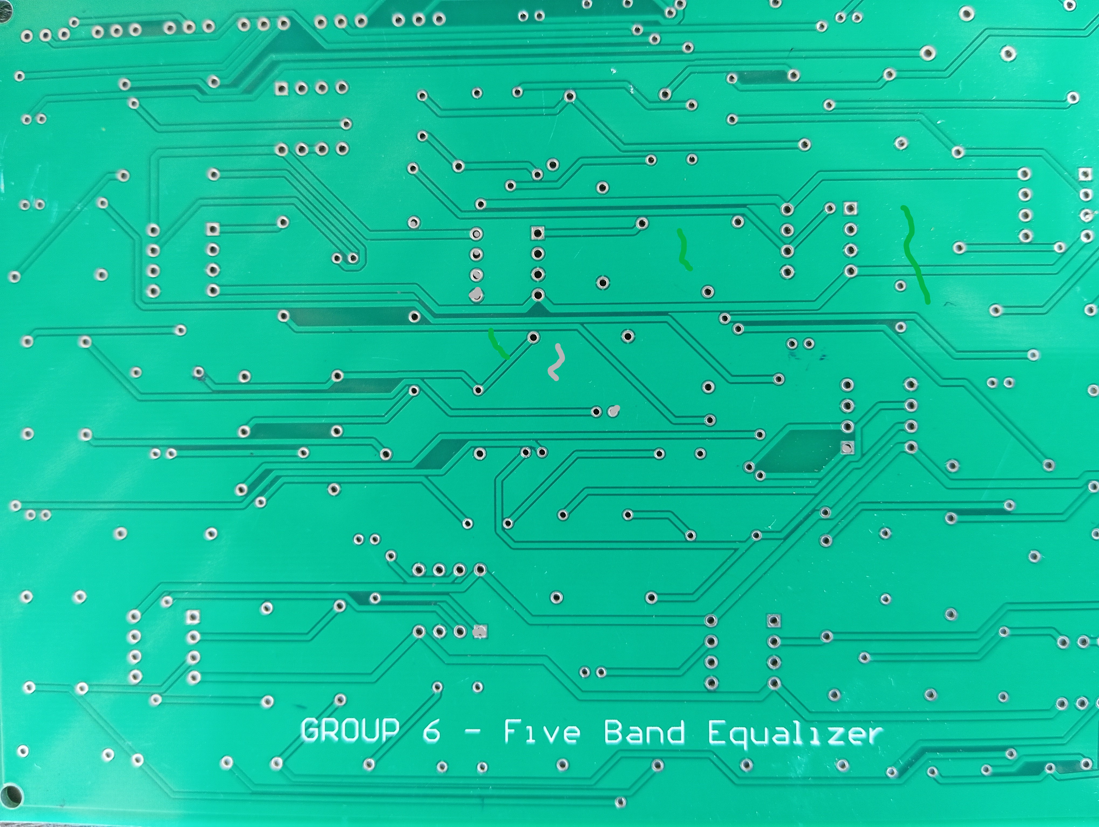
code/Test Images/test1.jpg
