JulianSilva2001/PCB-Defects-Detetion-Device/code/Test Images/test2.jpg

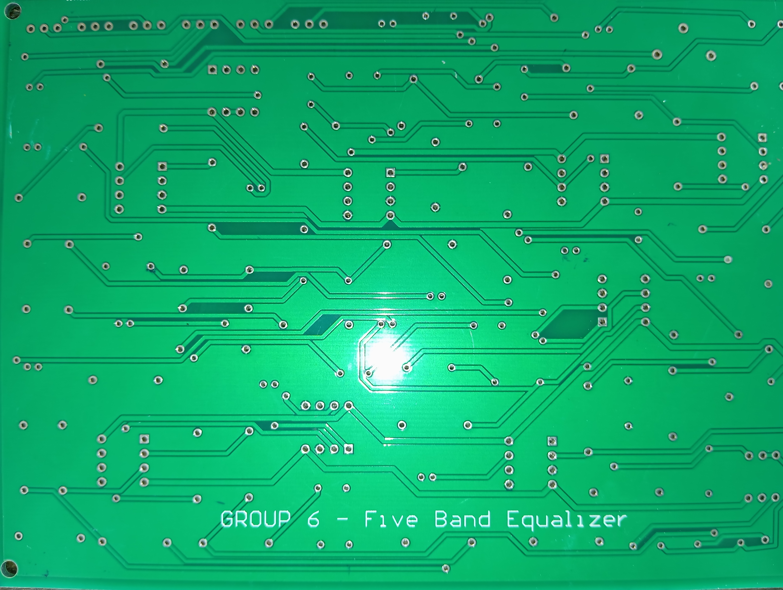
code/Test Images/test2.jpg
