JulianSilva2001/PCB-Defects-Detetion-Device/code/Test Images/test3.png

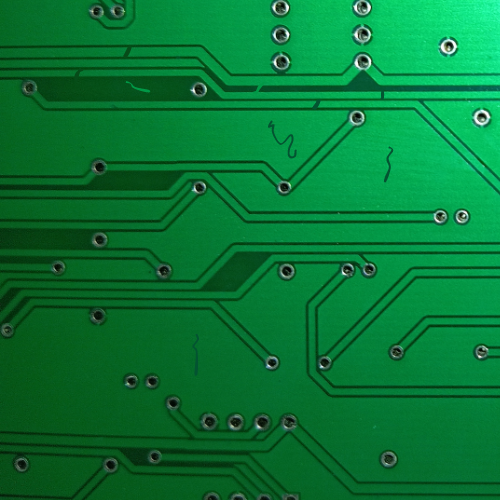
code/Test Images/test3.png
