JulianSilva2001/PCB-Defects-Detetion-Device/code/Test Images/WhatsApp Image 2024-08-16 at 13.32.02_2e965edd.jpg

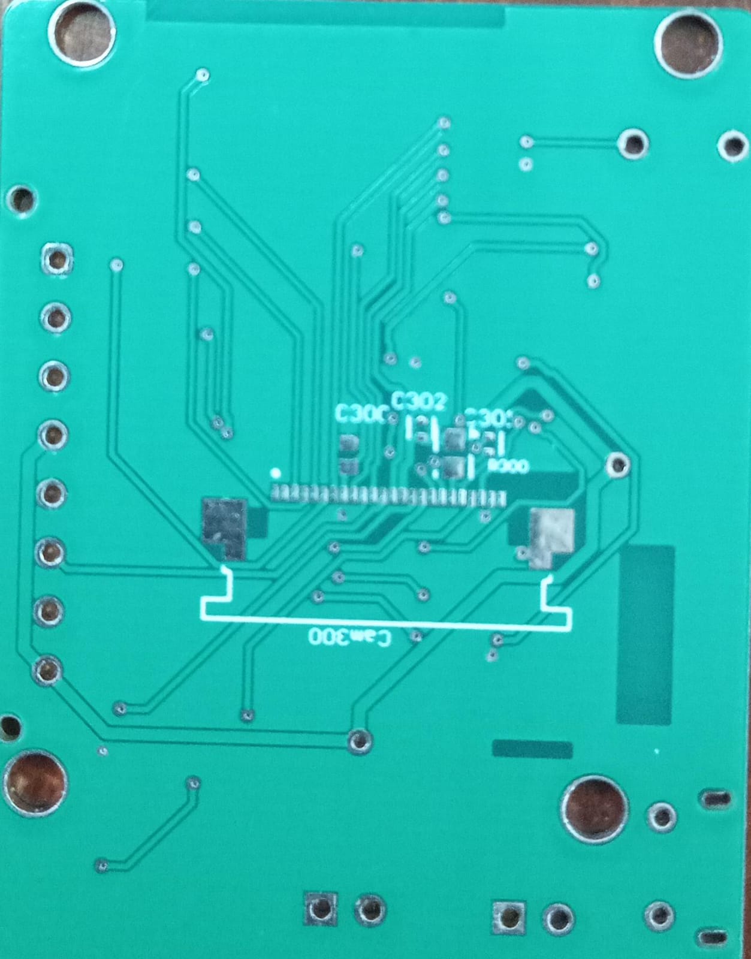
code/Test Images/WhatsApp Image 2024-08-16 at 13.32.02_2e965edd.jpg
