JulianSilva2001/PCB-Defects-Detetion-Device/code/Test Images/WhatsApp Image 2024-08-16 at 13.57.30_902c5983.jpg

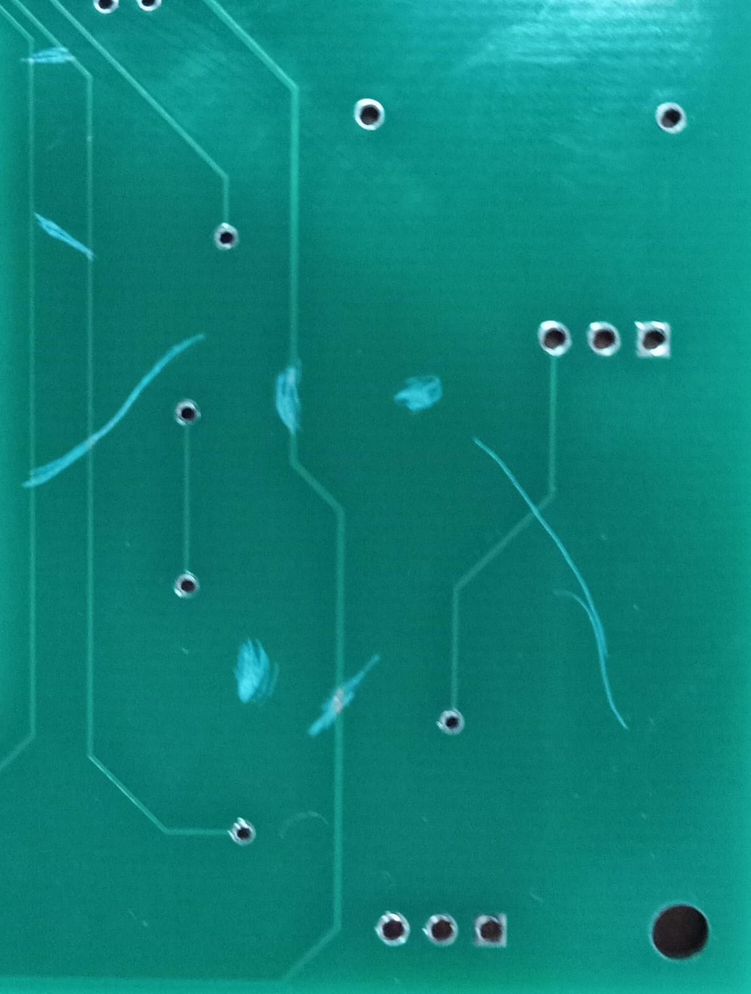
code/Test Images/WhatsApp Image 2024-08-16 at 13.57.30_902c5983.jpg
