JulianSilva2001/PCB-Defects-Detetion-Device/Model results/2a3c0fce-c061-4af3-9a84-7a4043674cfb.png

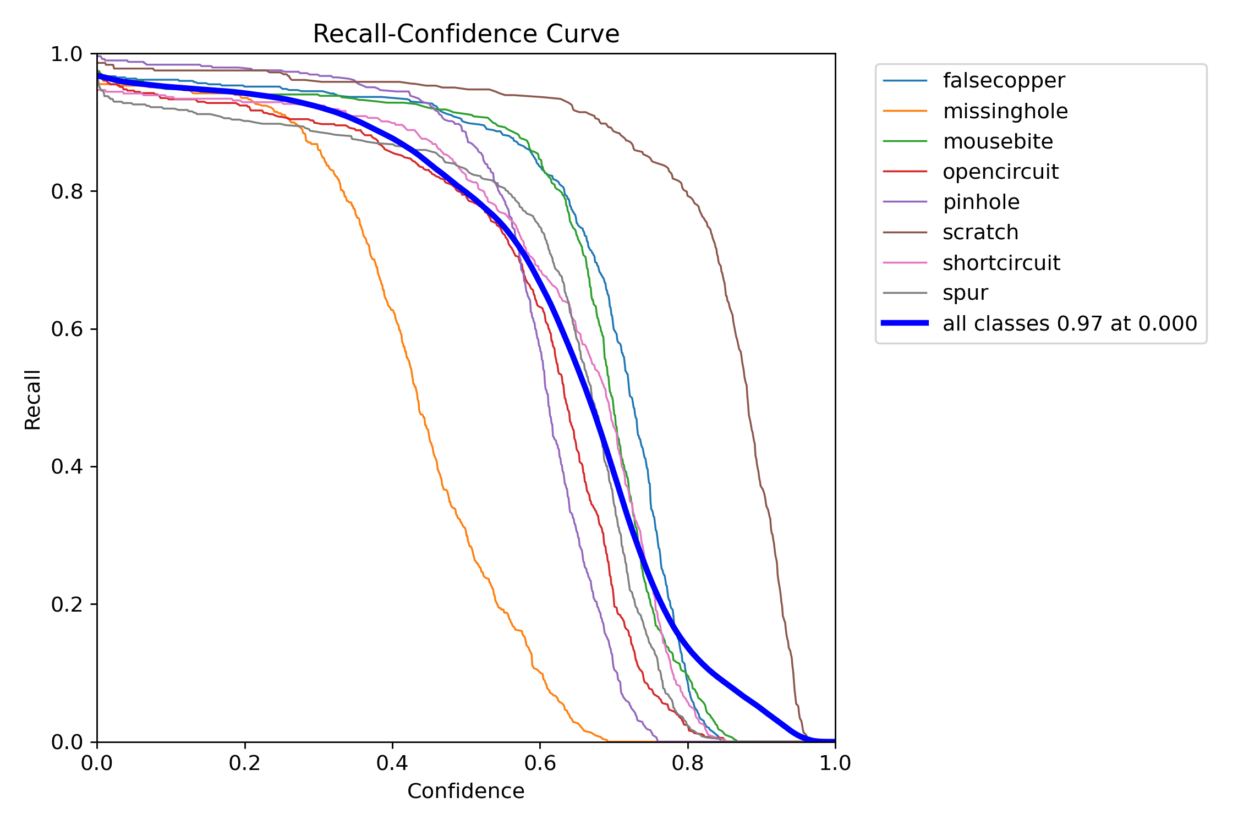
Model results/2a3c0fce-c061-4af3-9a84-7a4043674cfb.png
