JulianSilva2001/PCB-Defects-Detetion-Device/Model results/26b092fa-fb8c-46e1-bd88-5219416cb156.jpeg

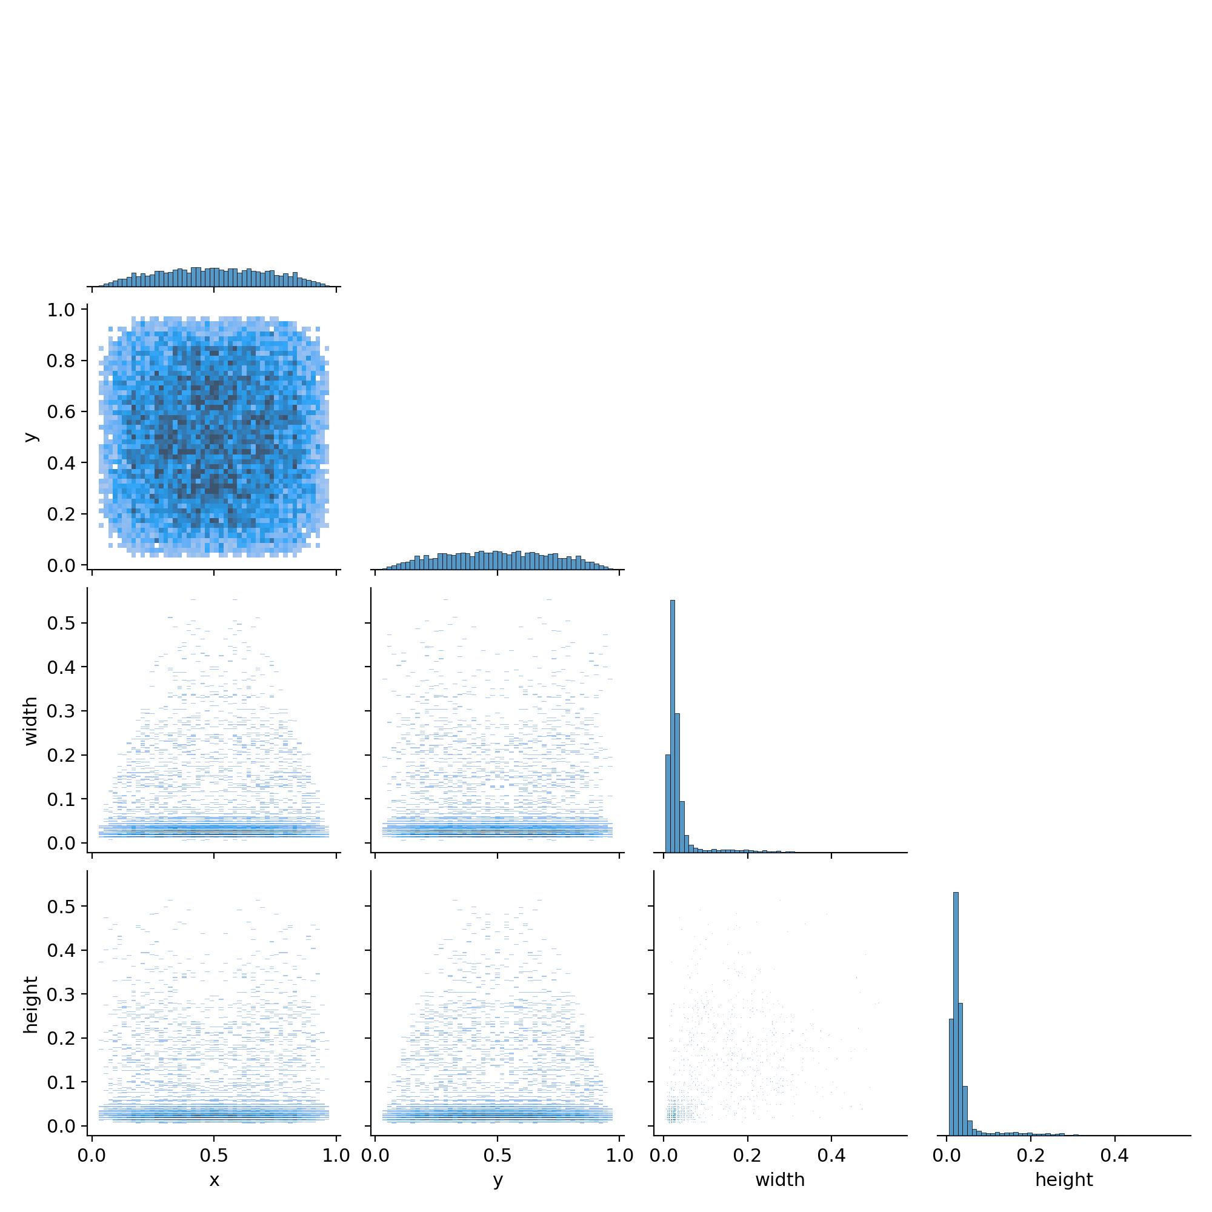
Model results/26b092fa-fb8c-46e1-bd88-5219416cb156.jpeg
