JulianSilva2001/PCB-Defects-Detetion-Device/Model results/28872f71-35f7-44dd-91b8-f7b29c1d4243.png

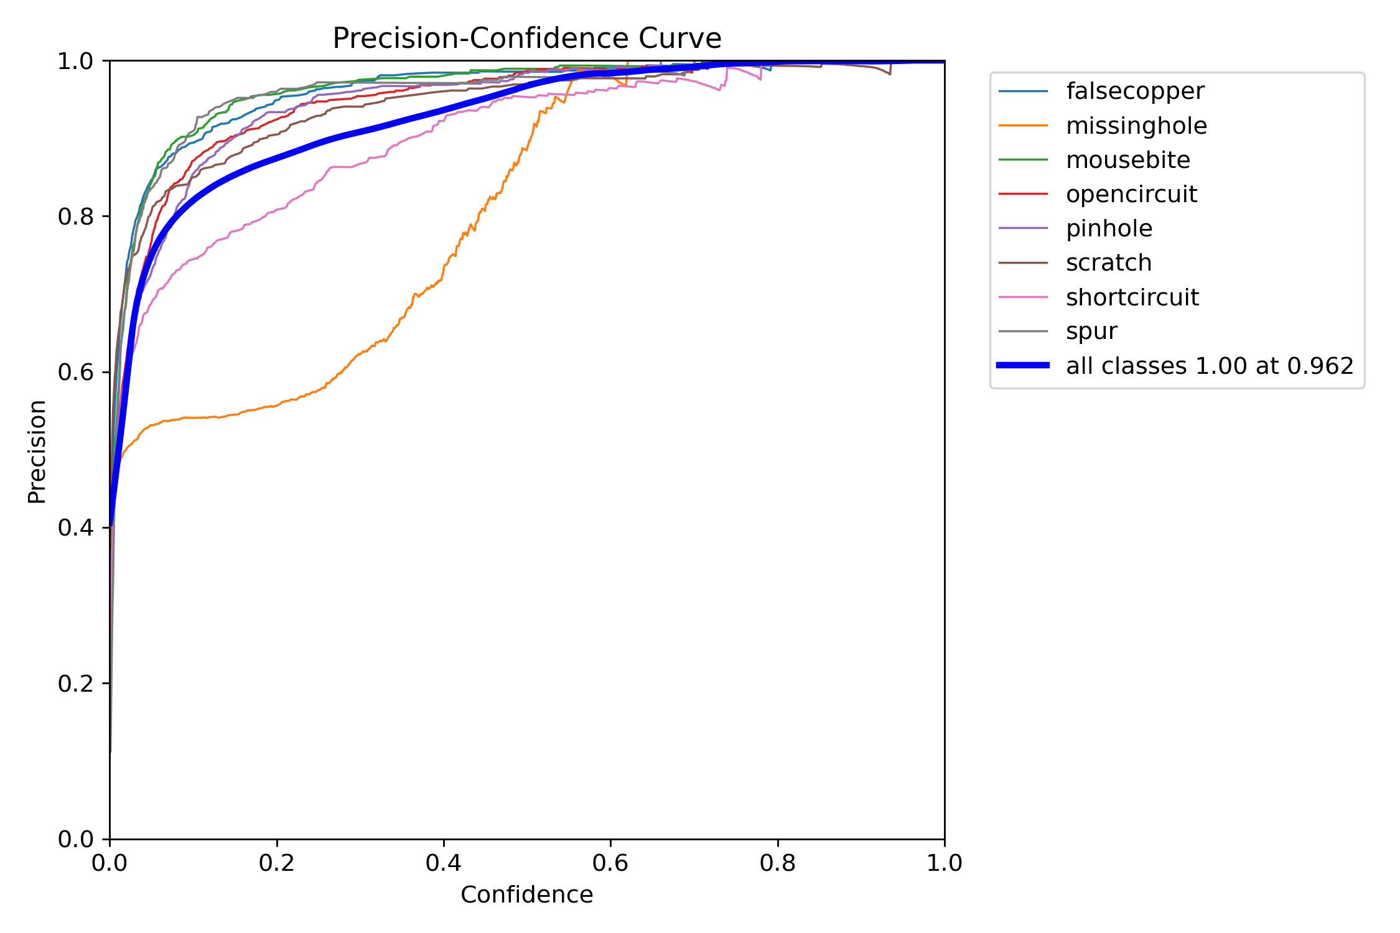
Model results/28872f71-35f7-44dd-91b8-f7b29c1d4243.png
