JulianSilva2001/PCB-Defects-Detetion-Device/Model results/ConfiedenceCurve.png

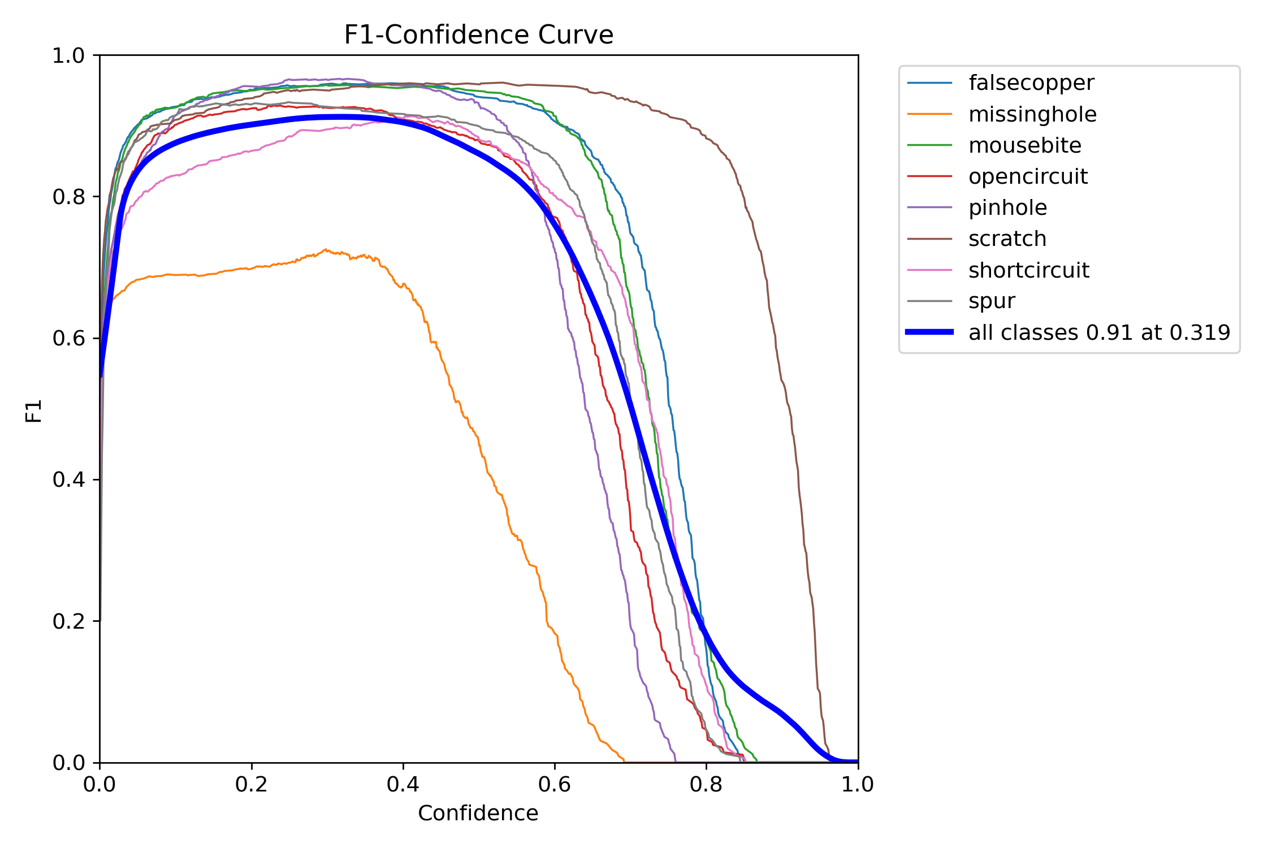
Model results/ConfiedenceCurve.png
