JulianSilva2001/PCB-Defects-Detetion-Device/Model results/confusion_matrix_normalized.png

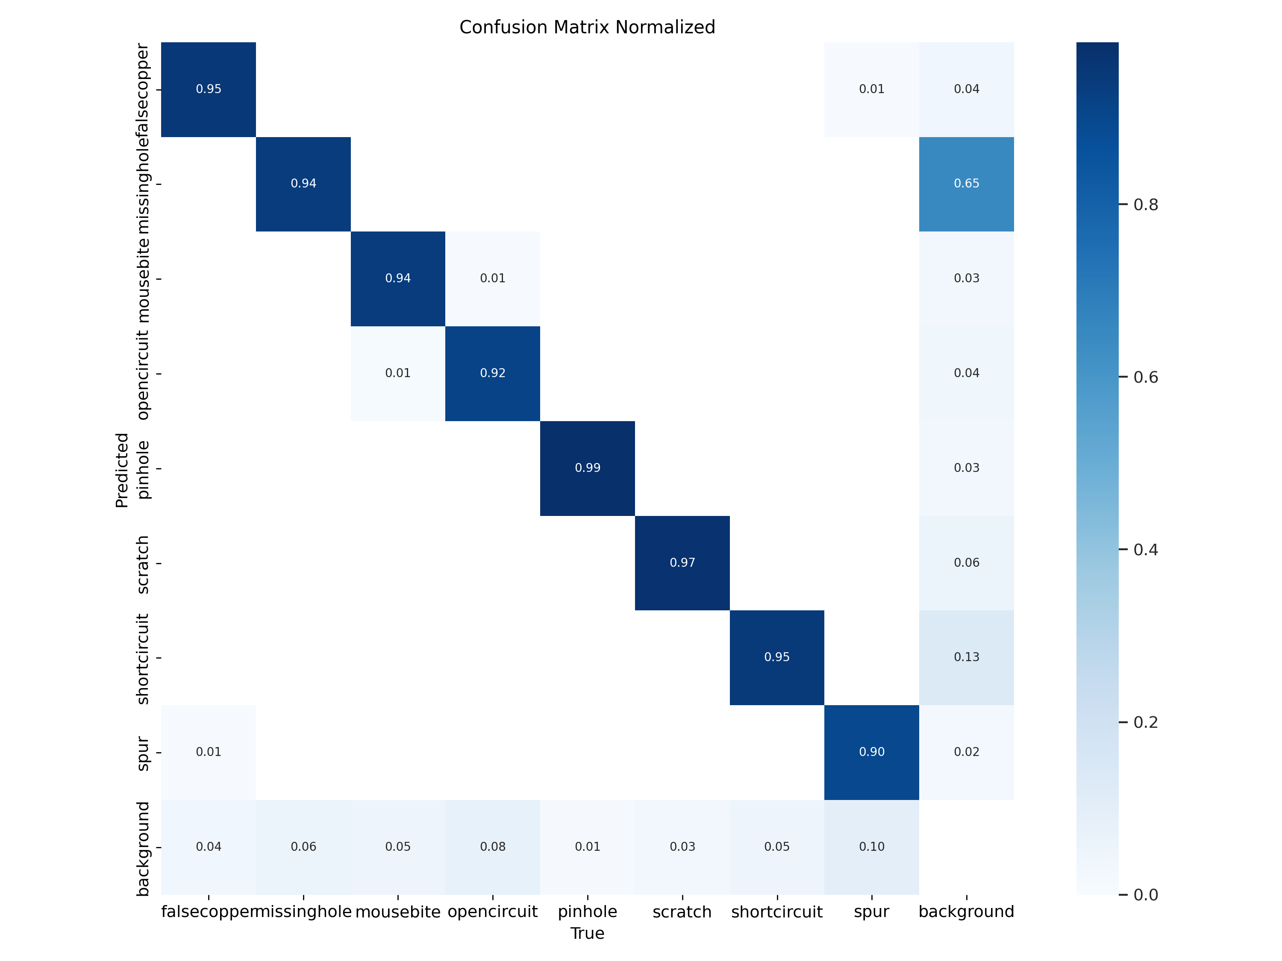
Model results/confusion_matrix_normalized.png
