JulianSilva2001/PCB-Defects-Detetion-Device/Model results/download (1).png

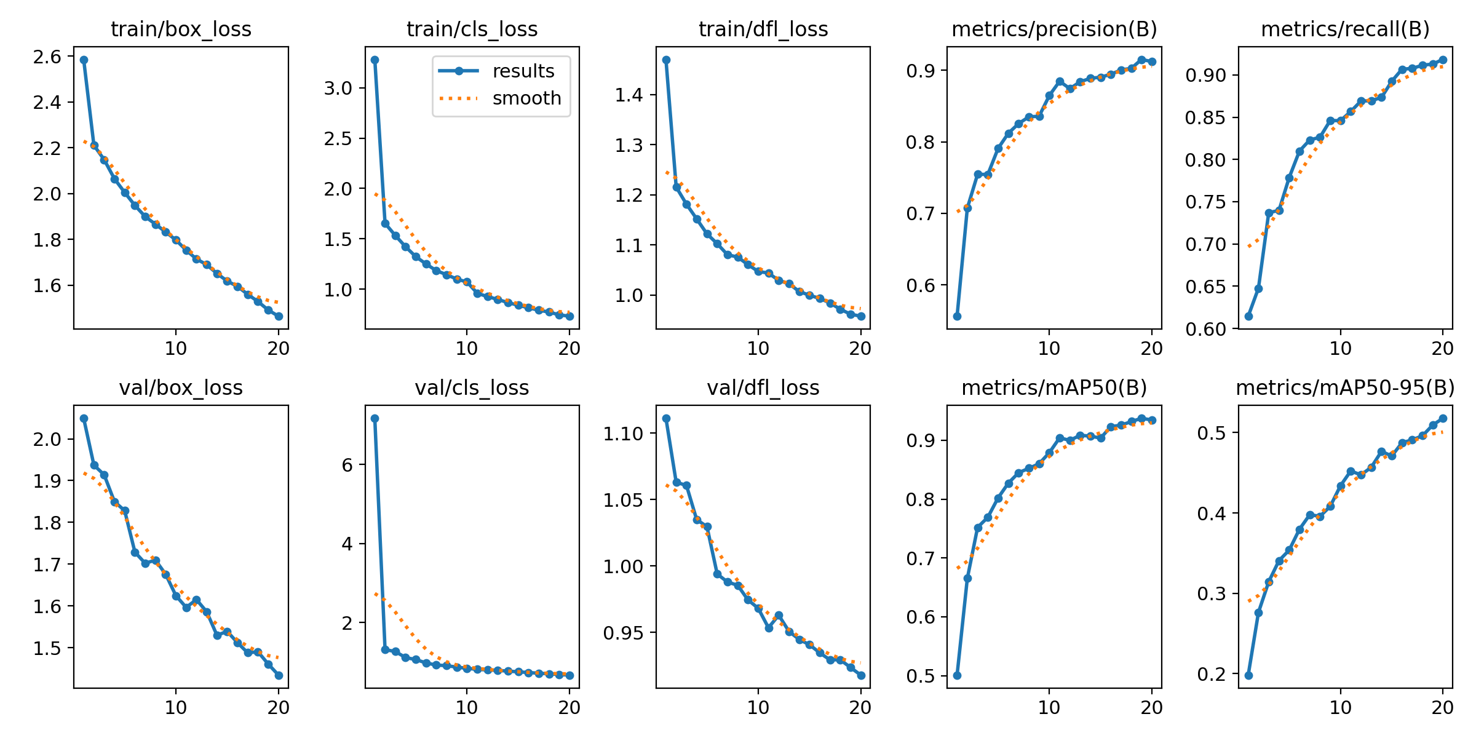
Model results/download (1).png
