JulianSilva2001/PCB-Defects-Detetion-Device/Model results/PrecisionRecallCurve.png

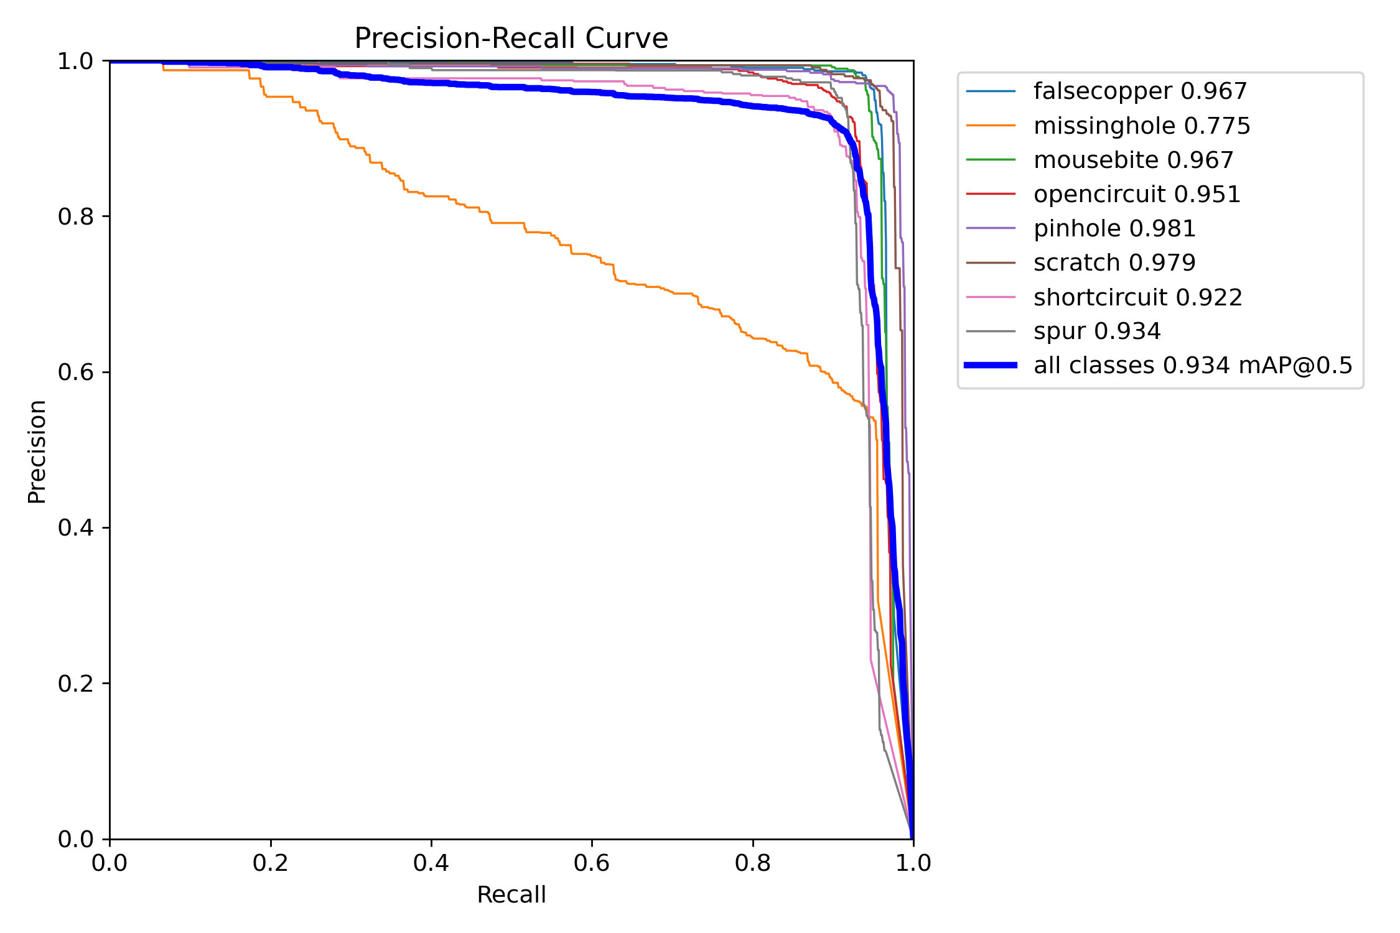
Model results/PrecisionRecallCurve.png
