JulianSilva2001/PCB-Defects-Detetion-Device/Model results/Spreading of Data.jpeg

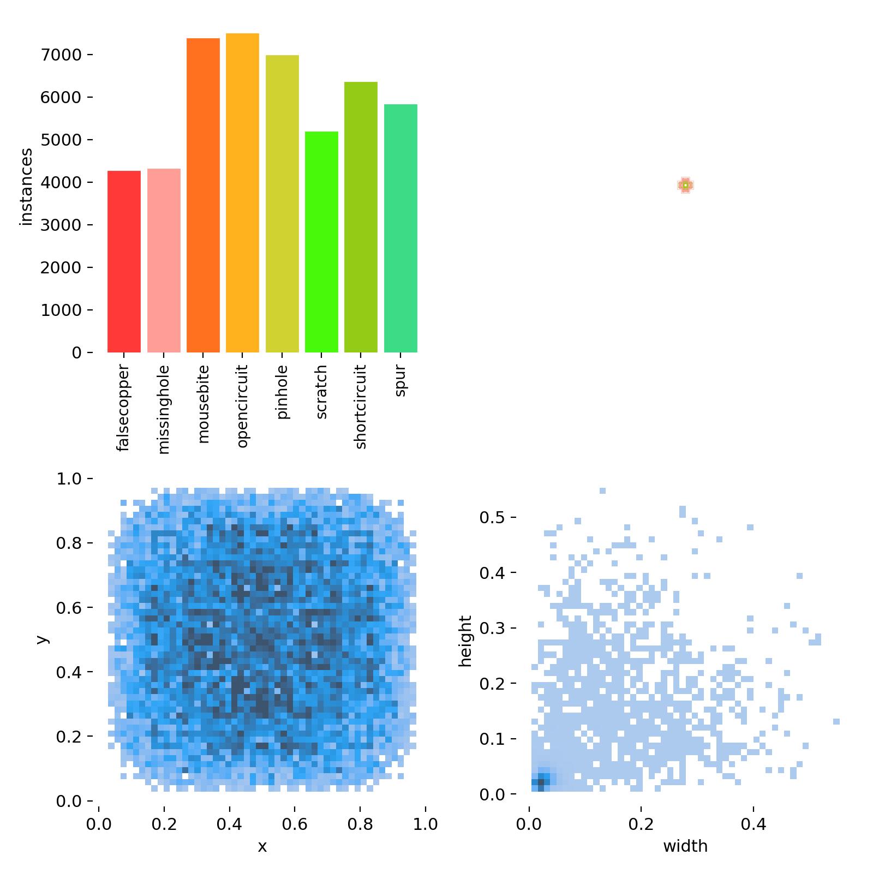
Model results/Spreading of Data.jpeg
