JulianSilva2001/PCB-Defects-Detetion-Device/Model results/val_batch2_labels.jpg

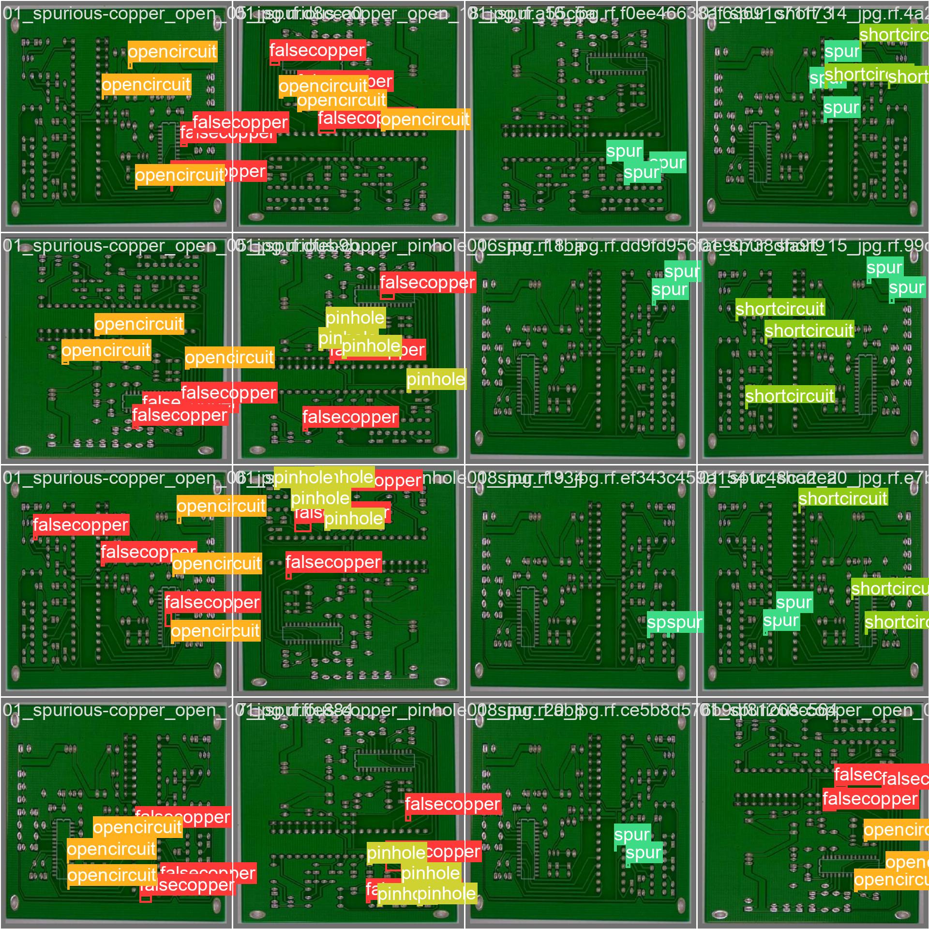
Model results/val_batch2_labels.jpg
