JulianSilva2001/PCB-Defects-Detetion-Device/runs/detect/predict2/test4.jpg

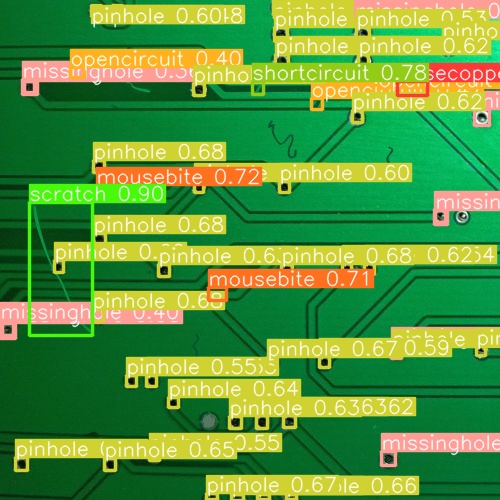
runs/detect/predict2/test4.jpg
