JulianSilva2001/PCB-Defects-Detetion-Device/runs/detect/predict3/test5.jpg

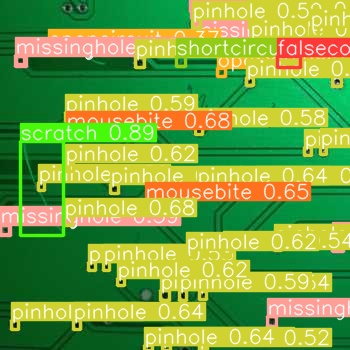
runs/detect/predict3/test5.jpg
