JulianSilva2001/PCB-Defects-Detetion-Device/runs/detect/predict4/test6.jpg

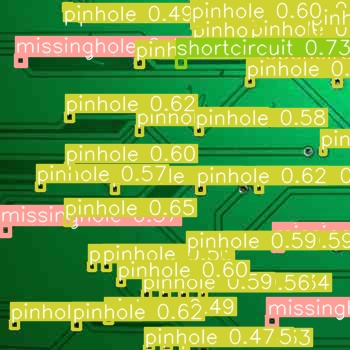
runs/detect/predict4/test6.jpg
