JulianSilva2001/PCB-Defects-Detetion-Device/runs/detect/predict/test3.png

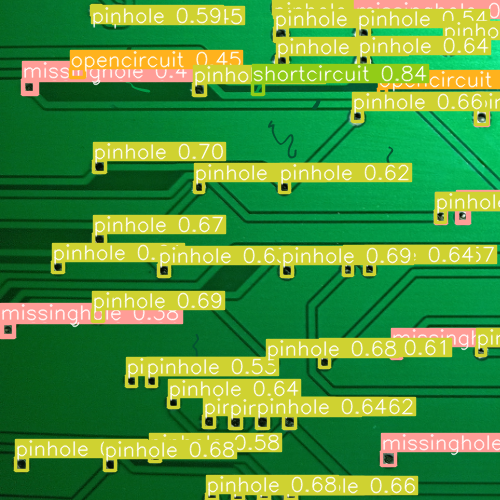
runs/detect/predict/test3.png
