JulianSilva2001/PCB-Defects-Detetion-Device/Test Results/3099ffe569334d1f577f252fb9f7fbcbd0ffd3ee89b0772e601eef2d.jpg

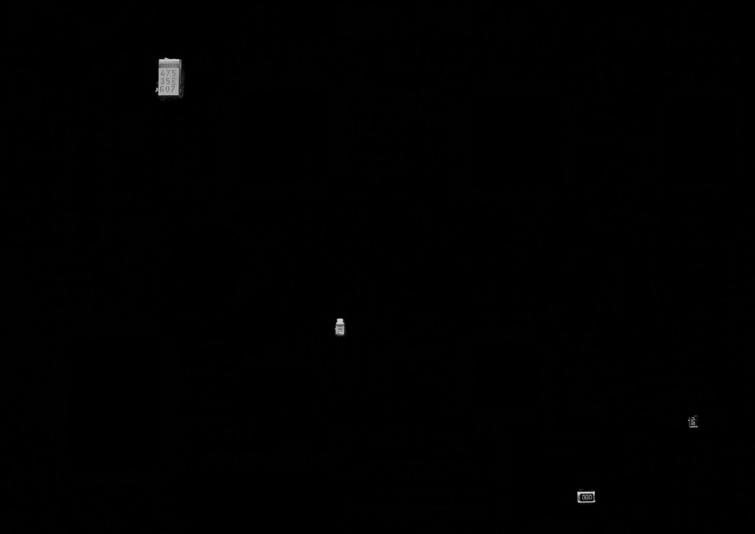
Test Results/3099ffe569334d1f577f252fb9f7fbcbd0ffd3ee89b0772e601eef2d.jpg
