JulianSilva2001/PCB-Defects-Detetion-Device/Test Results/Result_PCB_defects.jpg

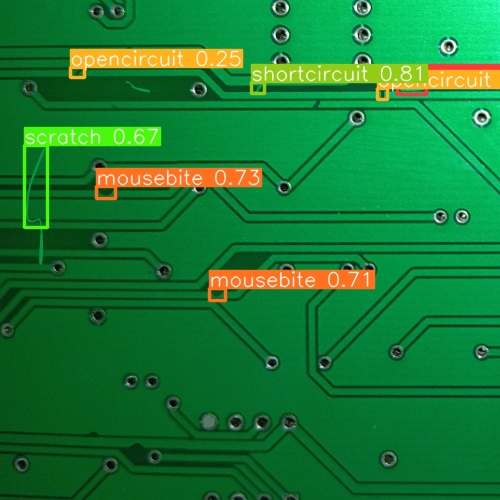
Test Results/Result_PCB_defects.jpg
