JulianSilva2001/PCB-Defects-Detetion-Device/Documentation/Image Doc/PCBtest1.jpg

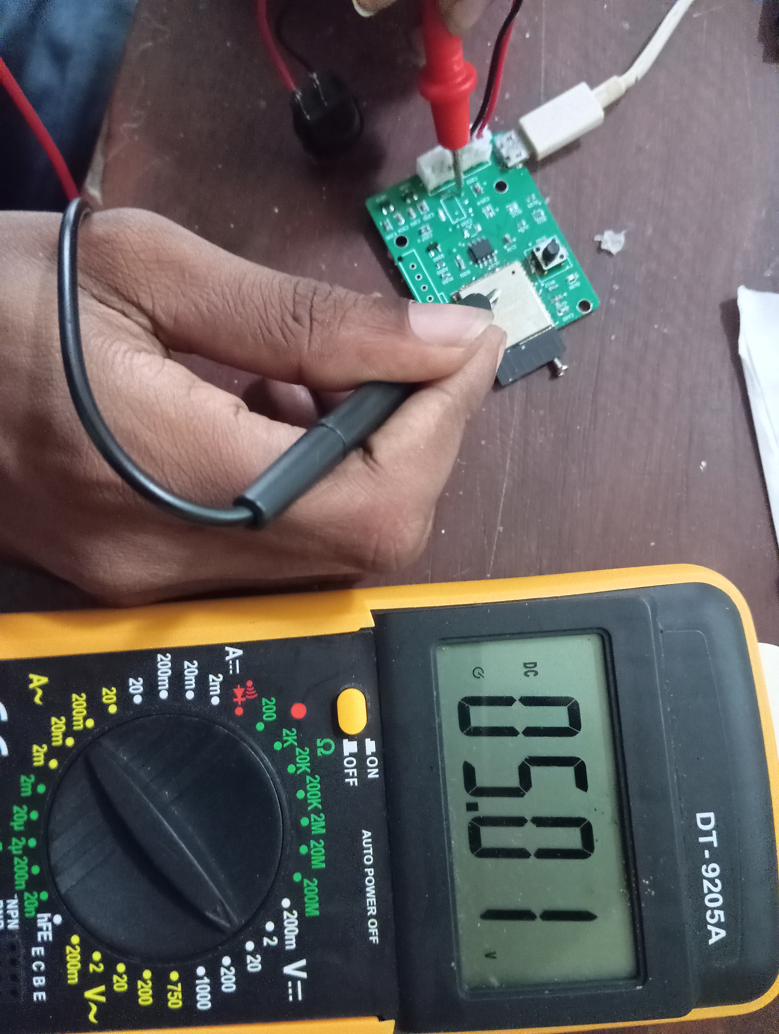
Documentation/Image Doc/PCBtest1.jpg
